RoboticsURJC/tfg-vdelatorre/memoria_tfg/portada/agradecimientos.tex

\cleardoublepage

\chapter*{Agradecimientos}

En primer lugar, quiero expresar mi gratitud a mi profesor, Julio Vega, por su apoyo y asesoramiento a lo largo de este proyecto. Sus conocimientos y recomendaciones fueron fundamentales para darle la dirección adecuada y obtener los resultados deseados.\\

A mis padres, gracias por su respaldo incondicional y por confiar en mí en cada etapa de mi formación académica.\\

Quiero agradecer también a mi hermana, mis amigos más cercanos y mi novia por sus ideas, consejos y por estar siempre ahí, brindándome su apoyo incondicional y motivación en todo momento.\\

Por último, me gustaría destacar la importancia de todos los recursos y fuentes que consulté durante la realización de este trabajo, así como de cualquier institución o persona que, de forma directa o indirecta, haya aportado a este proyecto.\\

Este trabajo es el resultado de cuatro años duros que no habrían resultado igual sin vosotros.\\
\ % Algo de separación...

\

\

\

\

\begin{flushright}
		\vspace{4.0 cm}
		\emph{A mi familia}\\
		\par
		\vspace{1.0 cm}
		Madrid, 2 de marzo de 2025\\ %\today
		\emph{Víctor de la Torre Rosa}
\end{flushright}

\thispagestyle{empty}
