RoboticsURJC/tfg-vdelatorre/memoria_tfg/portada/licencia.tex

% Este diseño se corresponde con la licencia CC-BY-NC-SA.
% Por supuesto, puedes poner la licencia que mejor se adapte al propósito de tu trabajo.
% Recuerda que, si no se especifica ninguna licencia, esta -como cualquier creación artística- pasaría a estar licenciada con todos los derechos reservados (copyright).

\cleardoublepage

\begin{flushright}
\begin{figure}
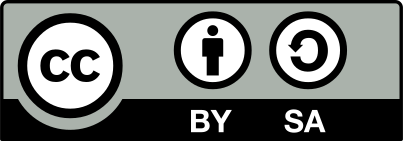
[picture p92: memoria_tfg/figs/by-sa.png]
 \ \ \ \ 
 \label{fig:cc} 
 \end{figure}
\end{flushright}

\

\

\

\noindent
Este trabajo se distribuye bajo los términos de la licencia internacional \href{http://creativecommons.org/licenses/by-sa/4.0/}{CC BY-SA International License} (Creative Commons Attribution-ShareAlike 4.0). Usted es libre de \textit{(a) compartir}: copiar y redistribuir el material en cualquier medio o formato para cualquier propósito, incluso comercialmente; y \textit{(b) adaptar}: remezclar, transformar y construir a partir del material para cualquier propósito, incluso comercialmente. La licenciante no puede revocar estas libertades en tanto usted siga los términos de la licencia:

\begin{itemize}
\item \textit{Atribución}. Usted debe dar \href{https://creativecommons.org/licenses/by-sa/4.0/deed.es#ref-appropriate-credit}{crédito de manera adecuada}, brindar un enlace a la licencia, e indicar \href{https://creativecommons.org/licenses/by-sa/4.0/deed.es#ref-indicate-changes}{si se han realizado cambios}. Puede hacerlo en cualquier forma razonable, pero no de forma tal que sugiera que usted o su uso tienen el apoyo de la licenciante.
\item \textit{Compartir igual}. Si remezcla, transforma o crea a partir del material, debe distribuir su contribución bajo la \href{https://creativecommons.org/licenses/by-sa/4.0/deed.es#ref-same-license}{misma licencia} del original.\\
No hay restricciones adicionales — No puede aplicar términos legales ni \href{https://creativecommons.org/licenses/by-sa/4.0/deed.es#ref-technological-measures}{medidas tecnológicas} que restrinjan legalmente a otras a hacer cualquier uso permitido por la licencia.
\end{itemize}

\begin{flushright}
		\vspace{7.0 cm}
		\emph{Documento de} \textbf{Víctor de la Torre Rosa}. % TODO: pon aquí tu nombre cuando hagas el documento
\end{flushright}
