RoboticsURJC/tfg-vdelatorre/Imagenes/2025-01-02-201215_1920x1080_scrot.png

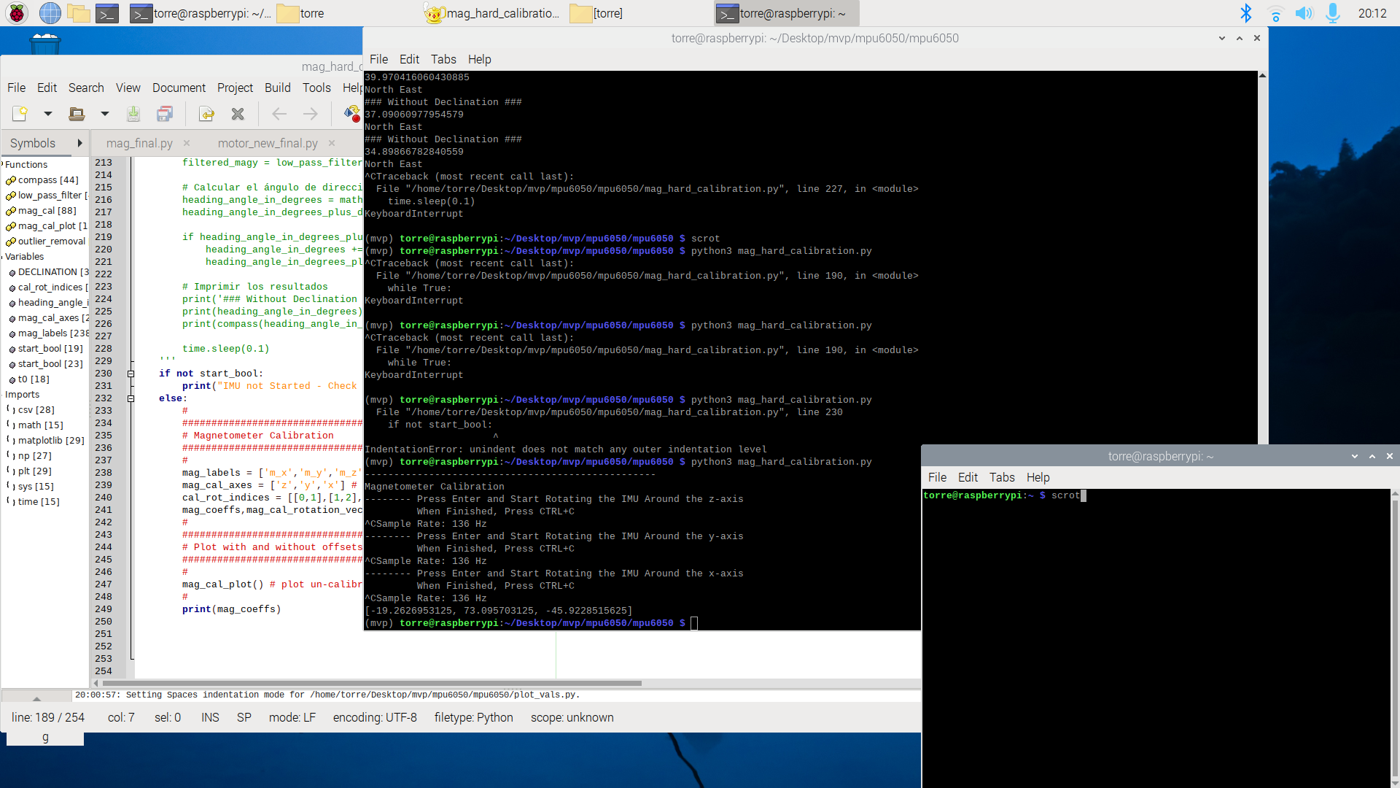
Imagenes/2025-01-02-201215_1920x1080_scrot.png
