RoboticsURJC/tfg-vdelatorre/Imagenes/aprox_pos_rasp.png

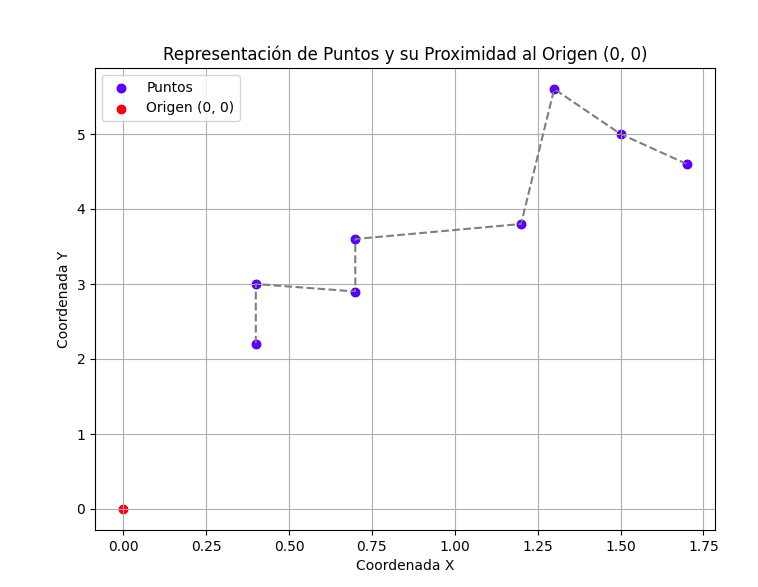
Imagenes/aprox_pos_rasp.png
