RoboticsURJC/tfg-vdelatorre/Imagenes/aps.jpeg

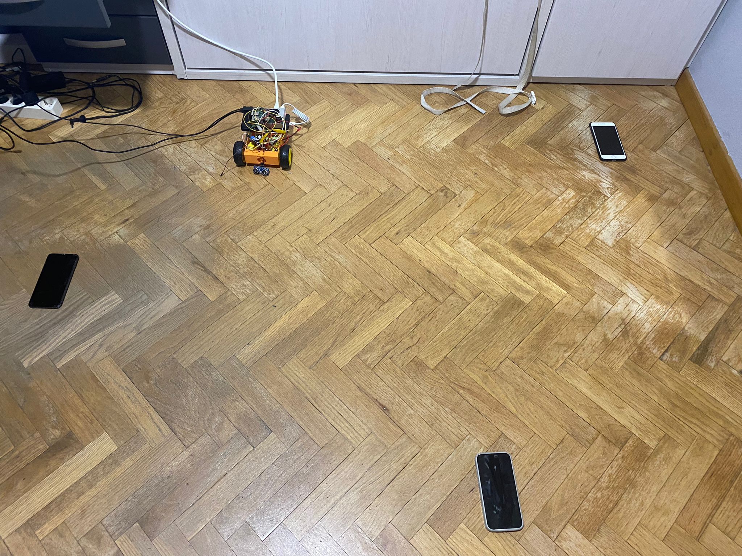
Imagenes/aps.jpeg
