RoboticsURJC/tfg-vdelatorre/Imagenes/astar2.png

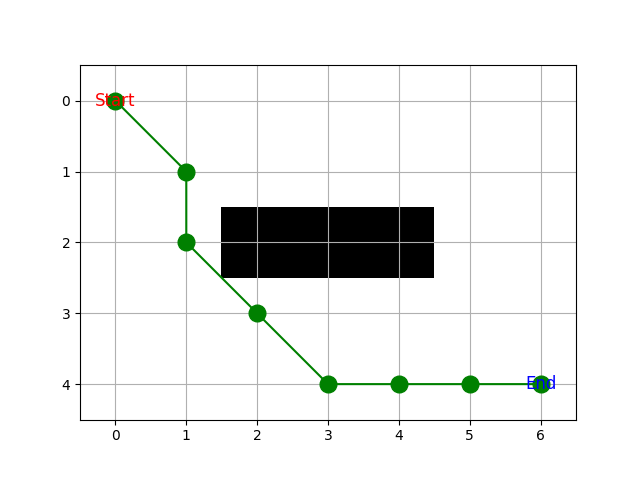
Imagenes/astar2.png
