RoboticsURJC/tfg-vdelatorre/Imagenes/astar3.png

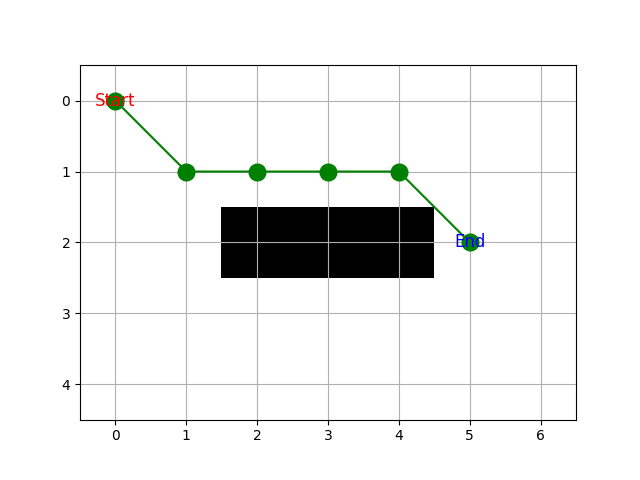
Imagenes/astar3.png
