RoboticsURJC/tfg-vdelatorre/Imagenes/astar5.png

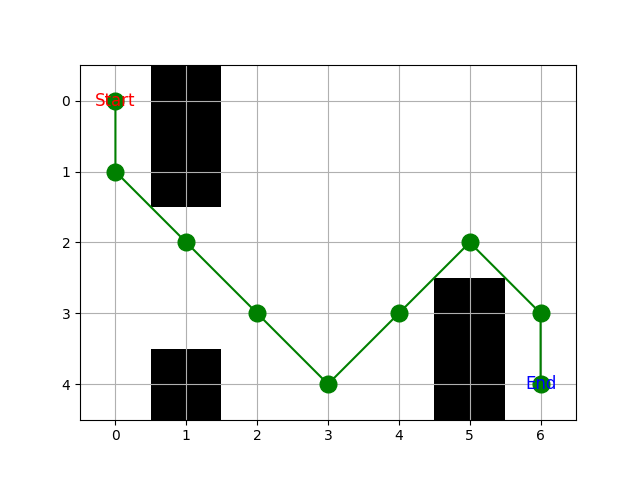
Imagenes/astar5.png
