RoboticsURJC/tfg-vdelatorre/Imagenes/astar.png

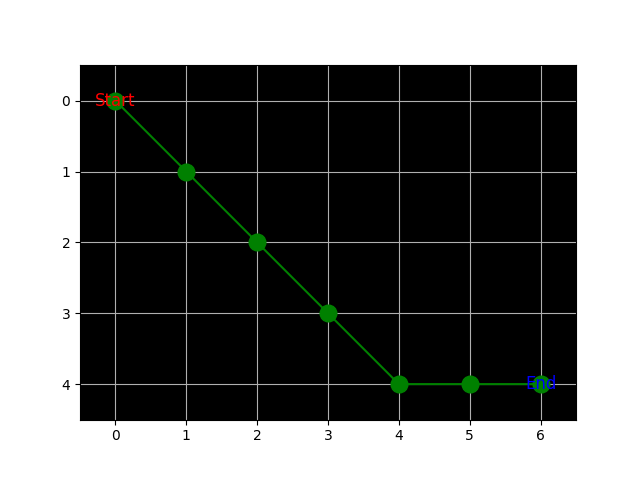
Imagenes/astar.png
