RoboticsURJC/tfg-vdelatorre/Imagenes/base_batería.png

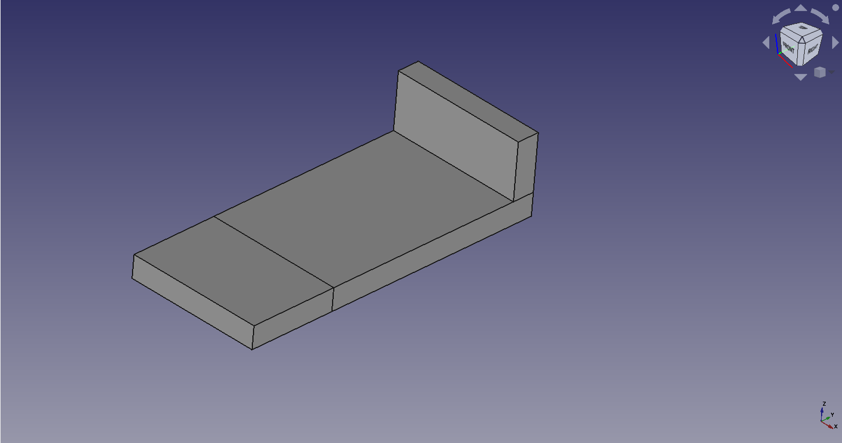
Imagenes/base_batería.png
