RoboticsURJC/tfg-vdelatorre/Imagenes/base_inicial_motor.png

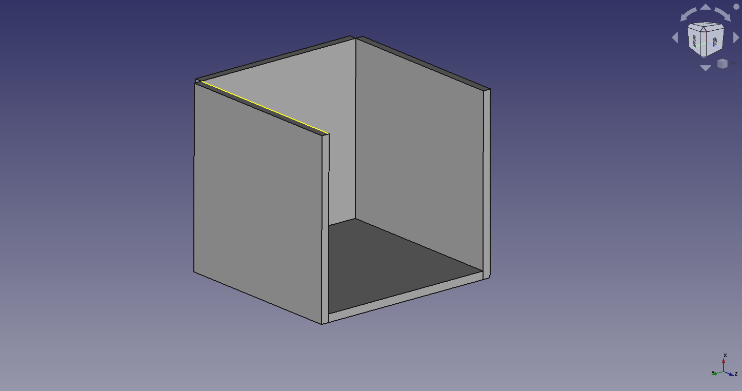
Imagenes/base_inicial_motor.png
