RoboticsURJC/tfg-vdelatorre/Imagenes/binary_text.png

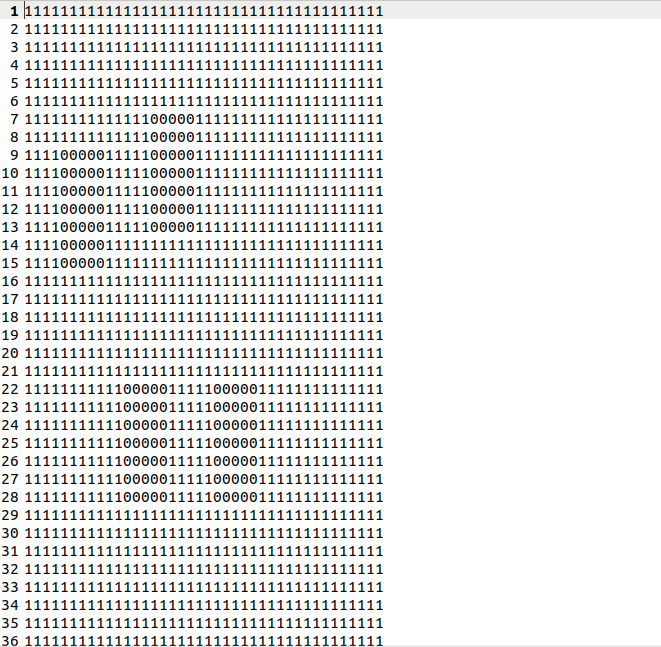
Imagenes/binary_text.png
