RoboticsURJC/tfg-vdelatorre/Imagenes/blog_2020_Raspberry_Pi4_Pi3B_00.jpg

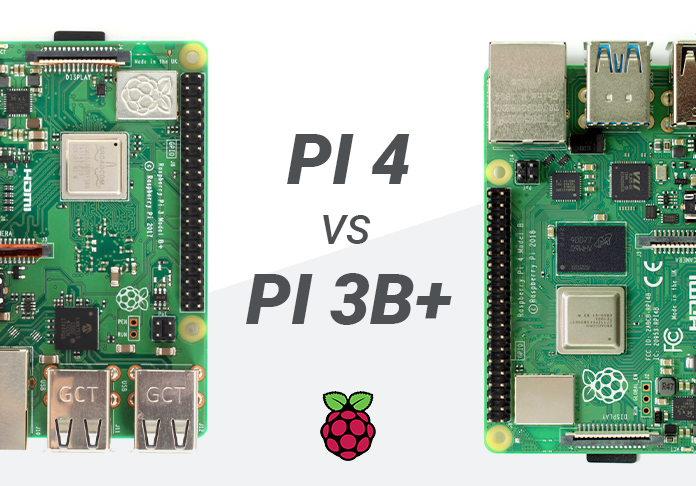
Imagenes/blog_2020_Raspberry_Pi4_Pi3B_00.jpg
