RoboticsURJC/tfg-vdelatorre/Imagenes/bola_loca.jpeg

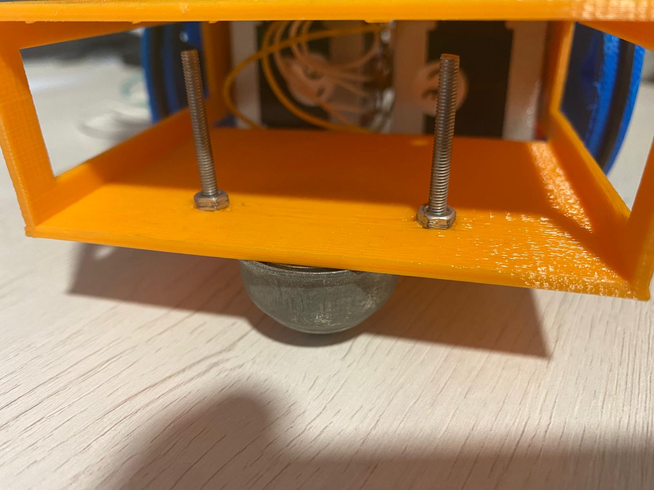
Imagenes/bola_loca.jpeg
