RoboticsURJC/tfg-vdelatorre/Imagenes/confusion_matrix.png

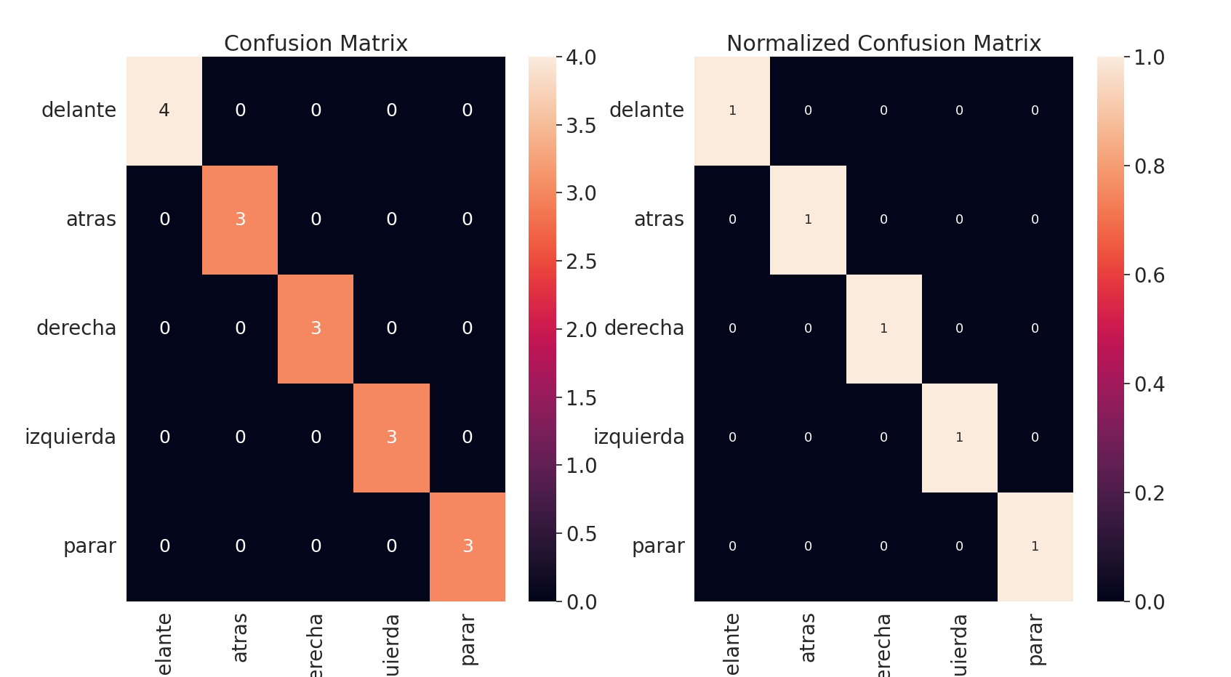
Imagenes/confusion_matrix.png
