RoboticsURJC/tfg-vdelatorre/Imagenes/dataset_add.png

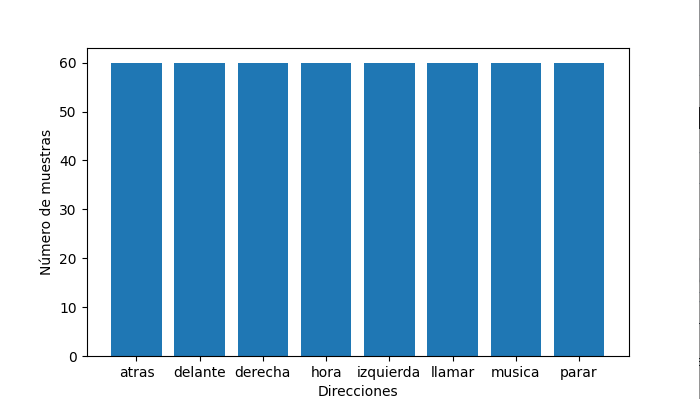
Imagenes/dataset_add.png
