RoboticsURJC/tfg-vdelatorre/Imagenes/datos_revista.png

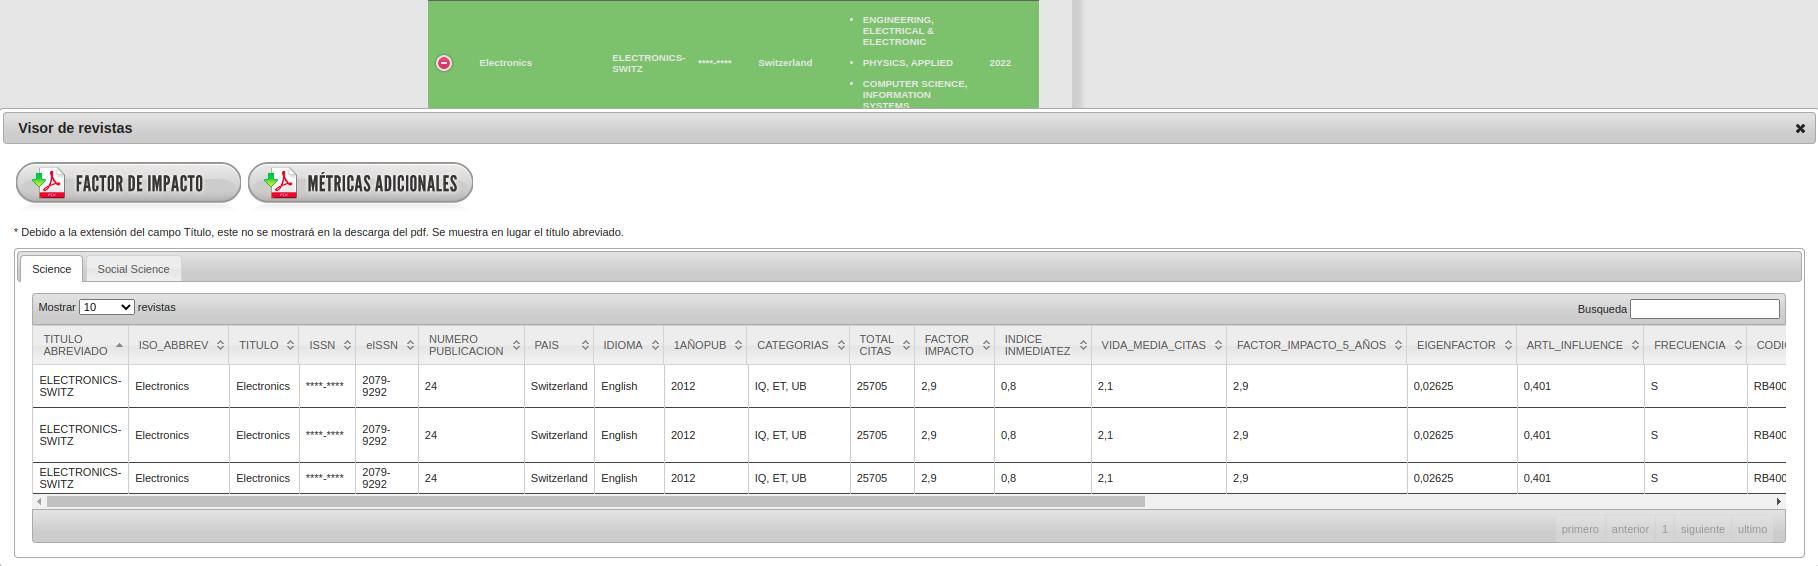
Imagenes/datos_revista.png
