RoboticsURJC/tfg-vdelatorre/Imagenes/driver_motor.jpeg

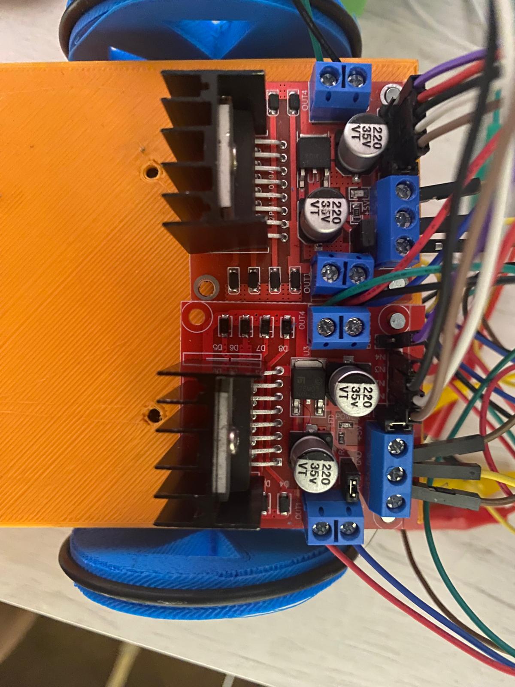
Imagenes/driver_motor.jpeg
