RoboticsURJC/tfg-vdelatorre/Imagenes/escalado_minmax_estandar.png

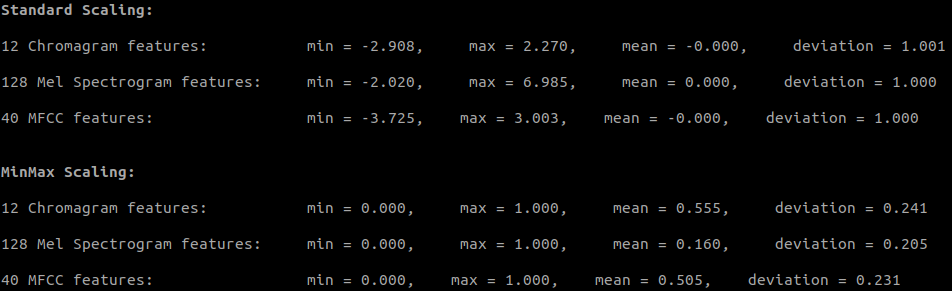
Imagenes/escalado_minmax_estandar.png
