RoboticsURJC/tfg-vdelatorre/Imagenes/fecyt.png

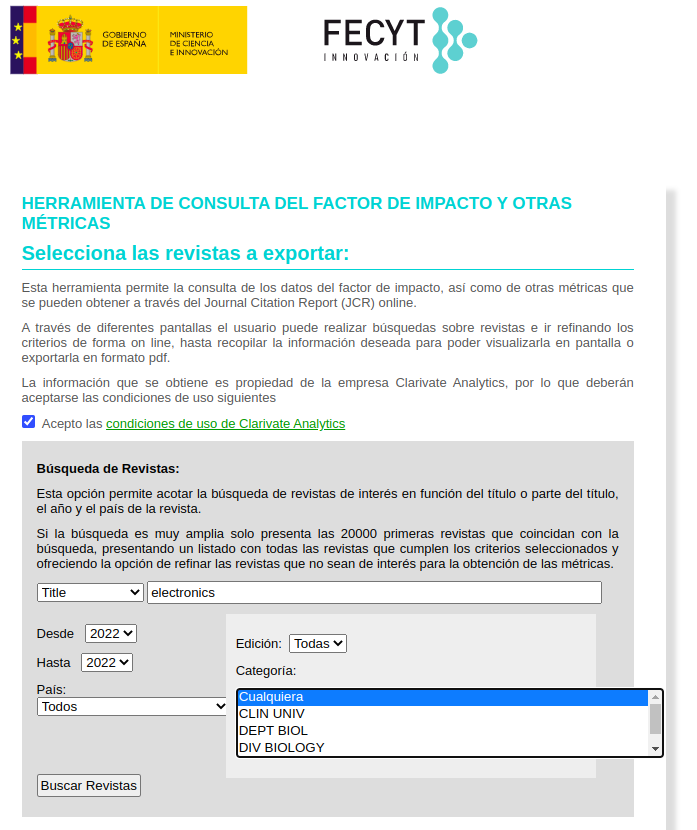
Imagenes/fecyt.png
