RoboticsURJC/tfg-vdelatorre/Imagenes/giroscopio.jpg

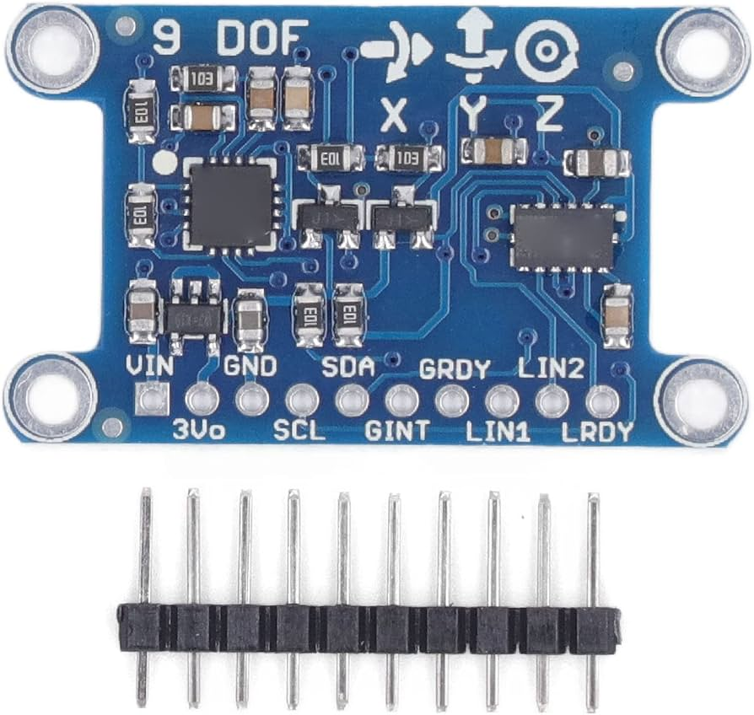
Imagenes/giroscopio.jpg
