RoboticsURJC/tfg-vdelatorre/Imagenes/google_scholar.png

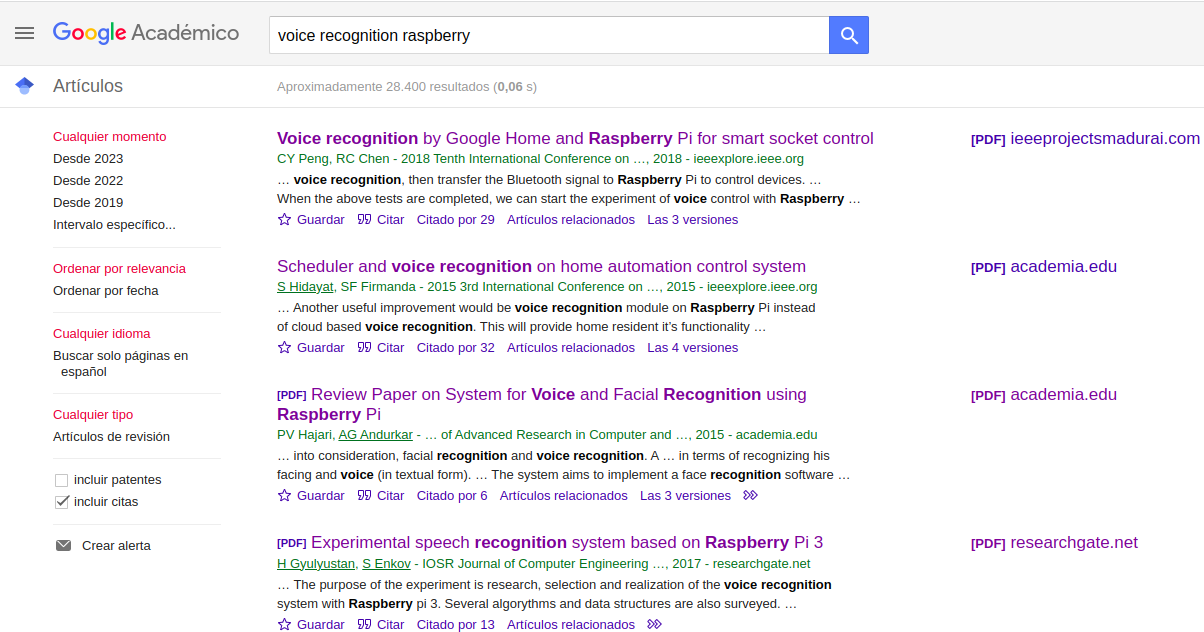
Imagenes/google_scholar.png
