RoboticsURJC/tfg-vdelatorre/Imagenes/gyros.png

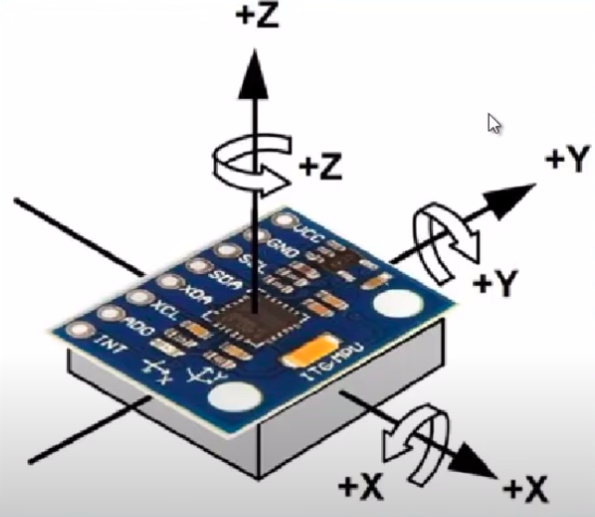
Imagenes/gyros.png
