RoboticsURJC/tfg-vdelatorre/Imagenes/imagen_motor_base.JPG

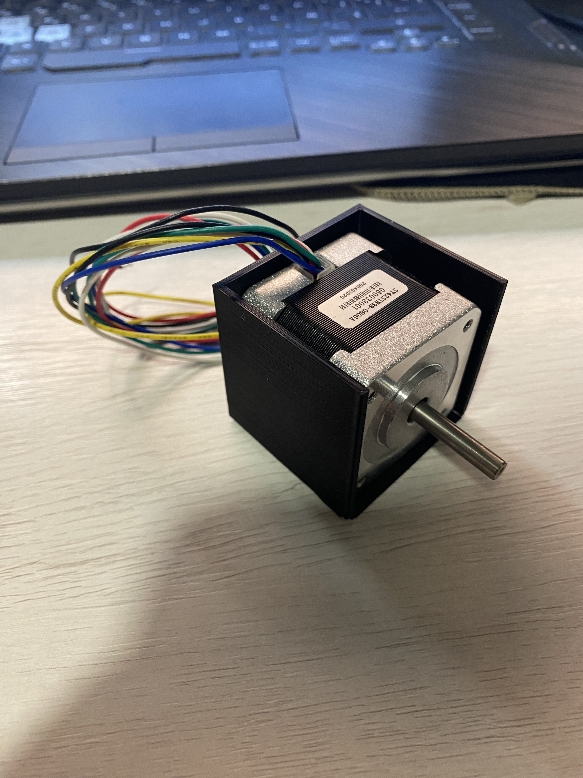
Imagenes/imagen_motor_base.JPG
