RoboticsURJC/tfg-vdelatorre/Imagenes/junta_rueda.jpeg

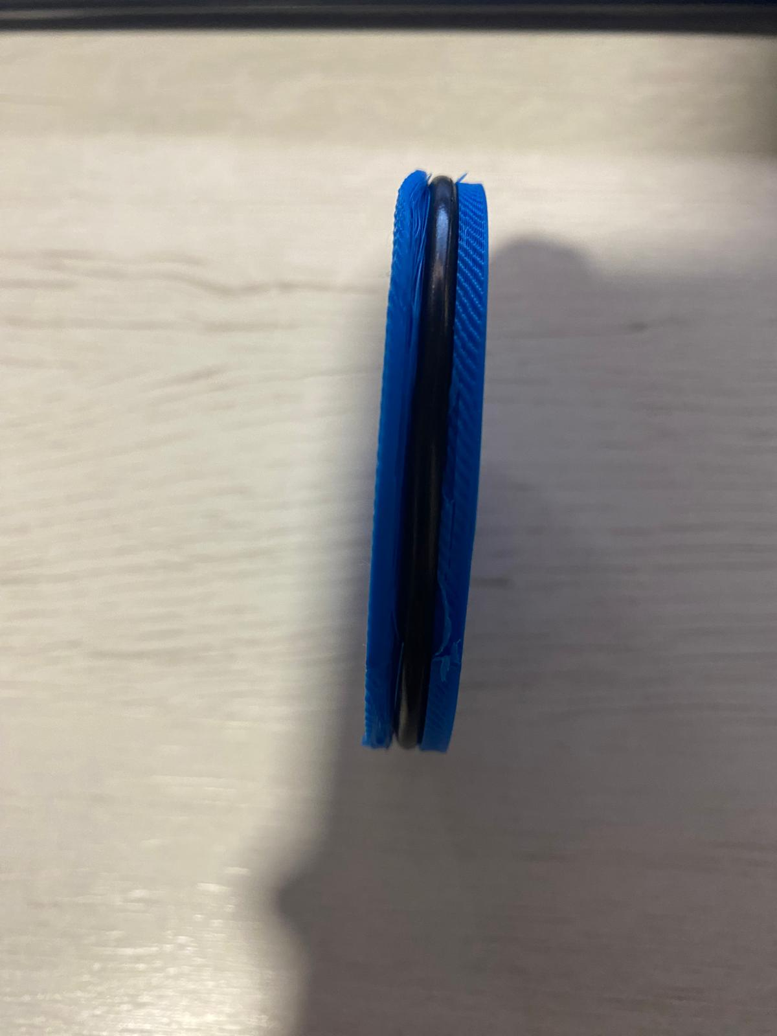
Imagenes/junta_rueda.jpeg
