RoboticsURJC/tfg-vdelatorre/Imagenes/l298n_bipolar_stepper_bb.png

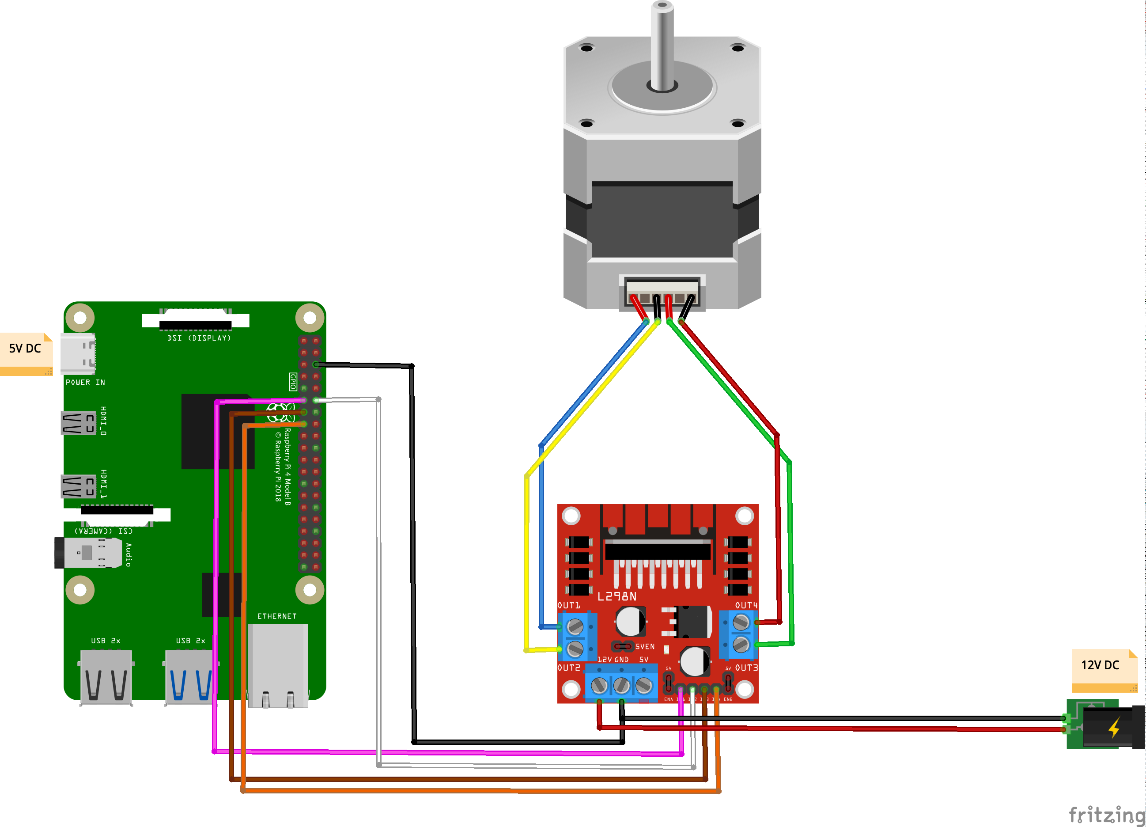
Imagenes/l298n_bipolar_stepper_bb.png
