RoboticsURJC/tfg-vdelatorre/Imagenes/map.png

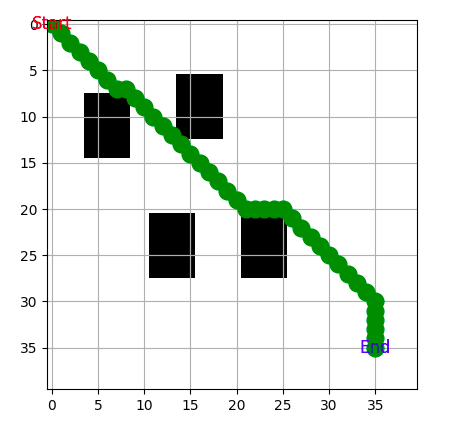
Imagenes/map.png
