RoboticsURJC/tfg-vdelatorre/Imagenes/map_color2.png

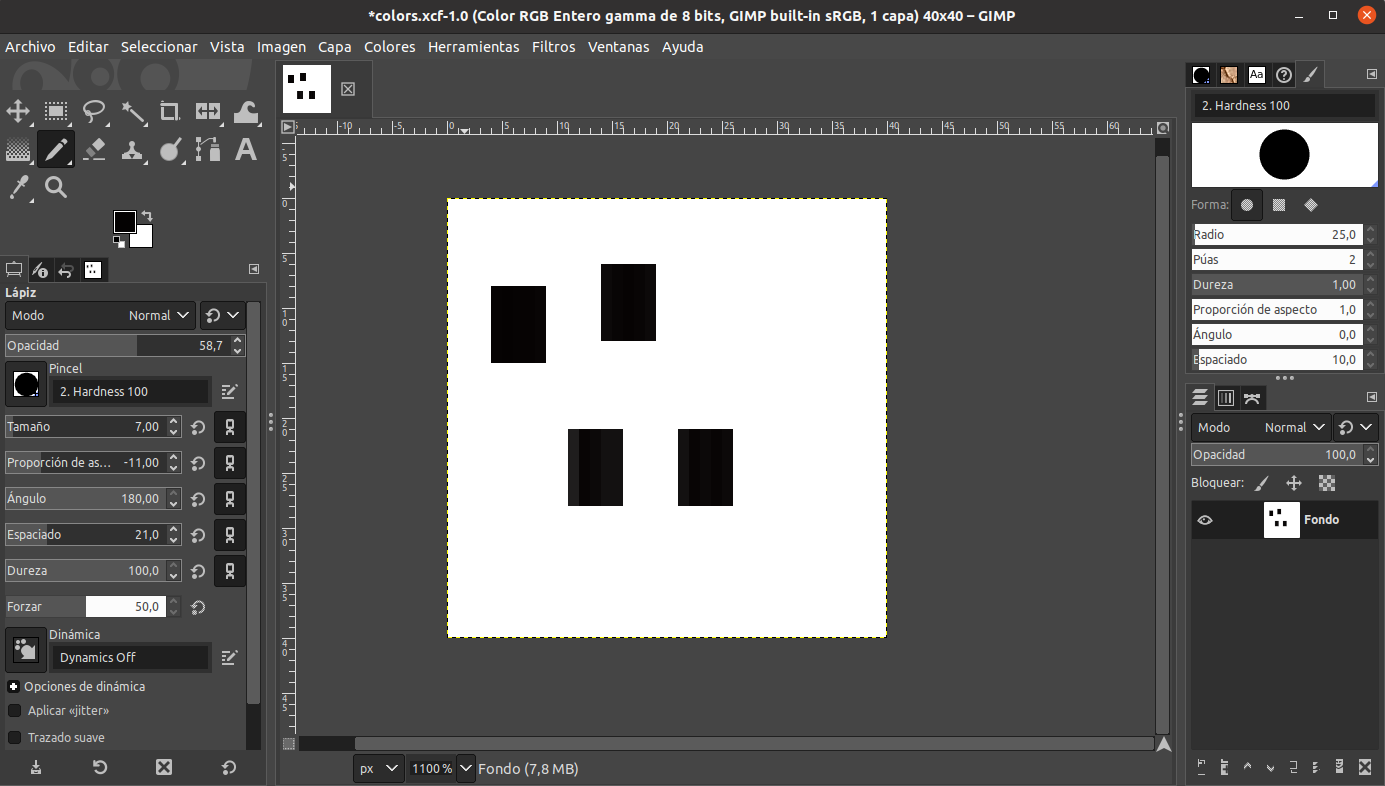
Imagenes/map_color2.png
