RoboticsURJC/tfg-vdelatorre/Imagenes/map_color.png

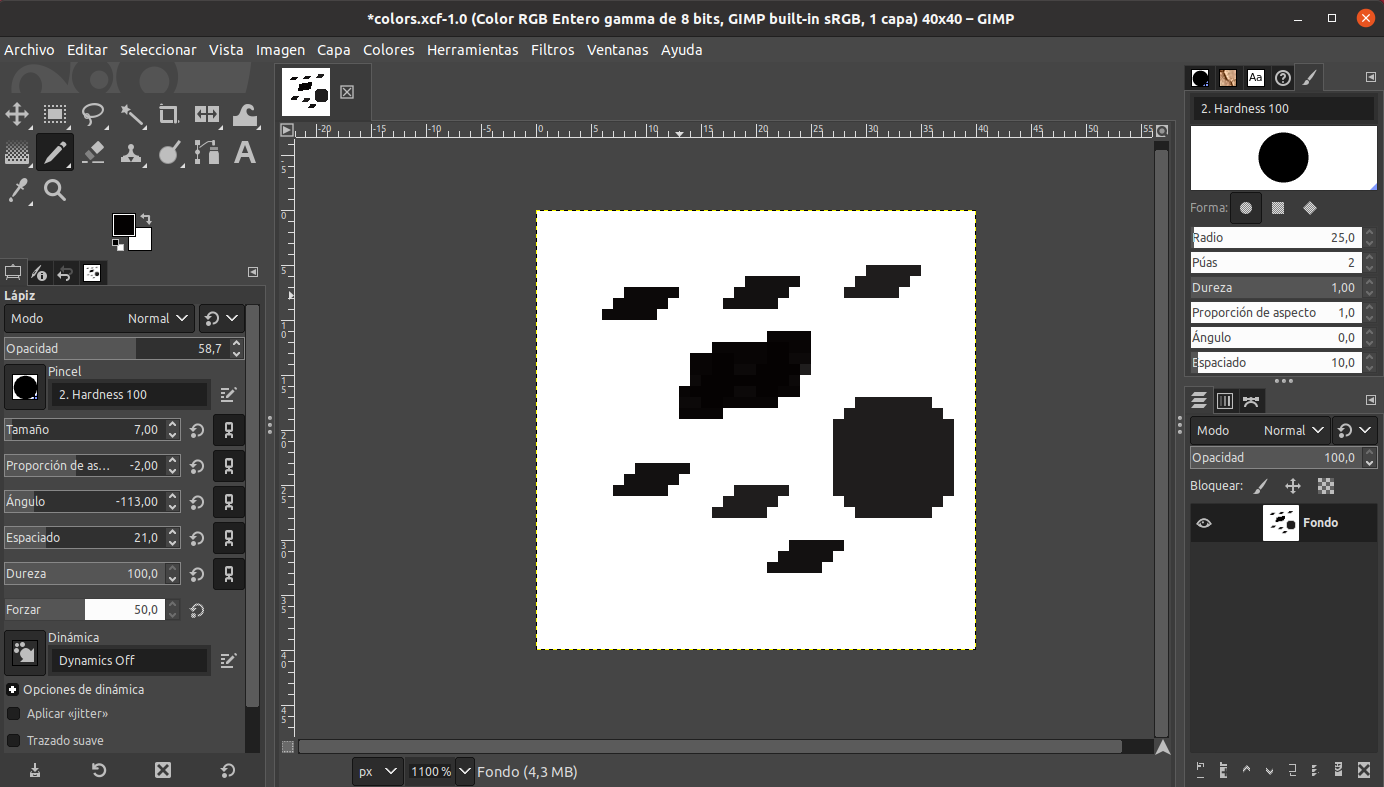
Imagenes/map_color.png
