RoboticsURJC/tfg-vdelatorre/Imagenes/matrix_features.png

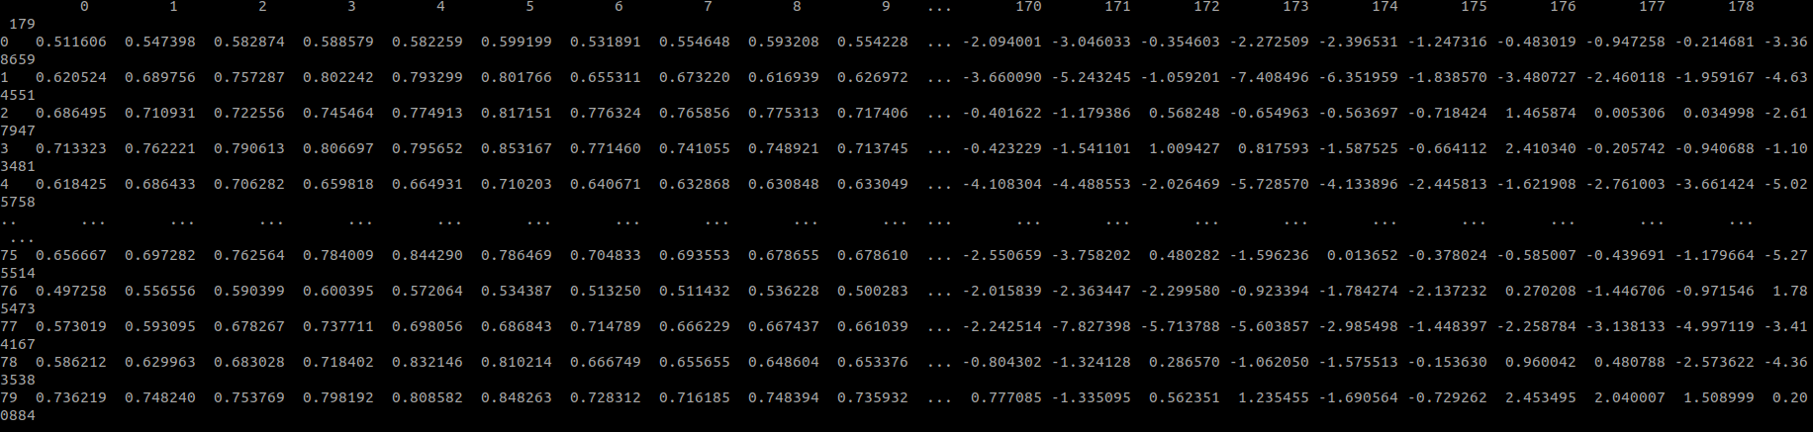
Imagenes/matrix_features.png
