RoboticsURJC/tfg-vdelatorre/Imagenes/matriz_confusion.png

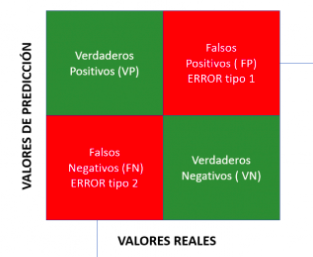
Imagenes/matriz_confusion.png
