RoboticsURJC/tfg-vdelatorre/Imagenes/modelo_silla_ruedas.png

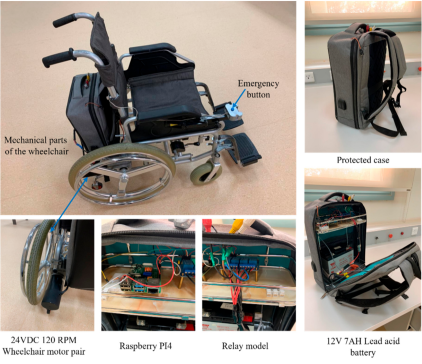
Imagenes/modelo_silla_ruedas.png
