RoboticsURJC/tfg-vdelatorre/Imagenes/motor1.jpg

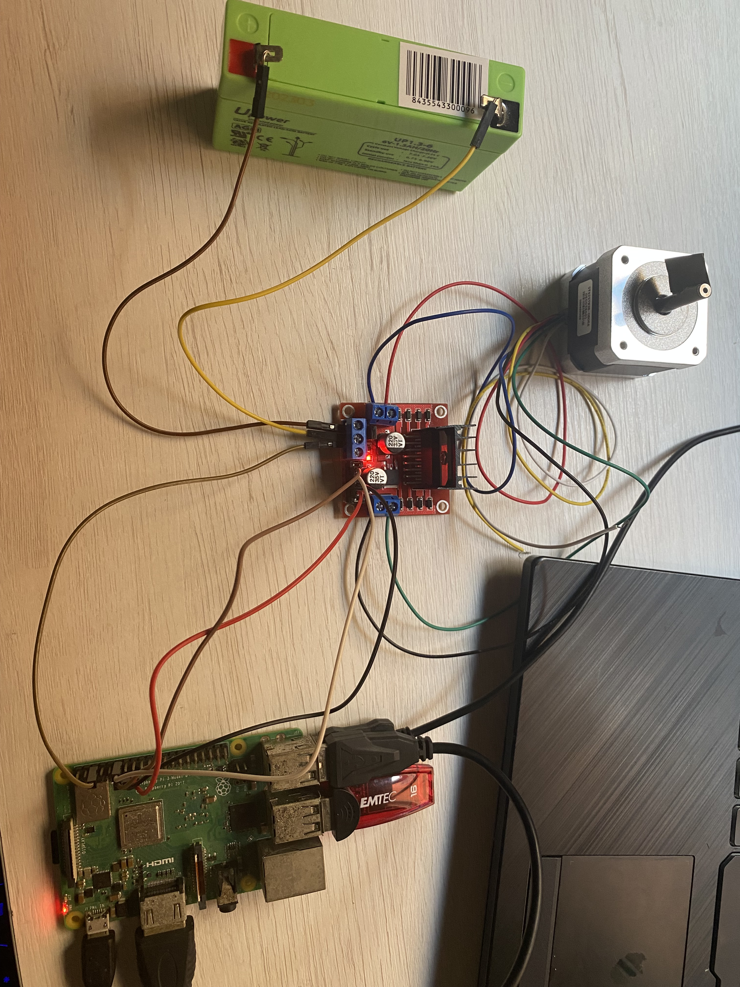
Imagenes/motor1.jpg
