RoboticsURJC/tfg-vdelatorre/Imagenes/motor2.jpg

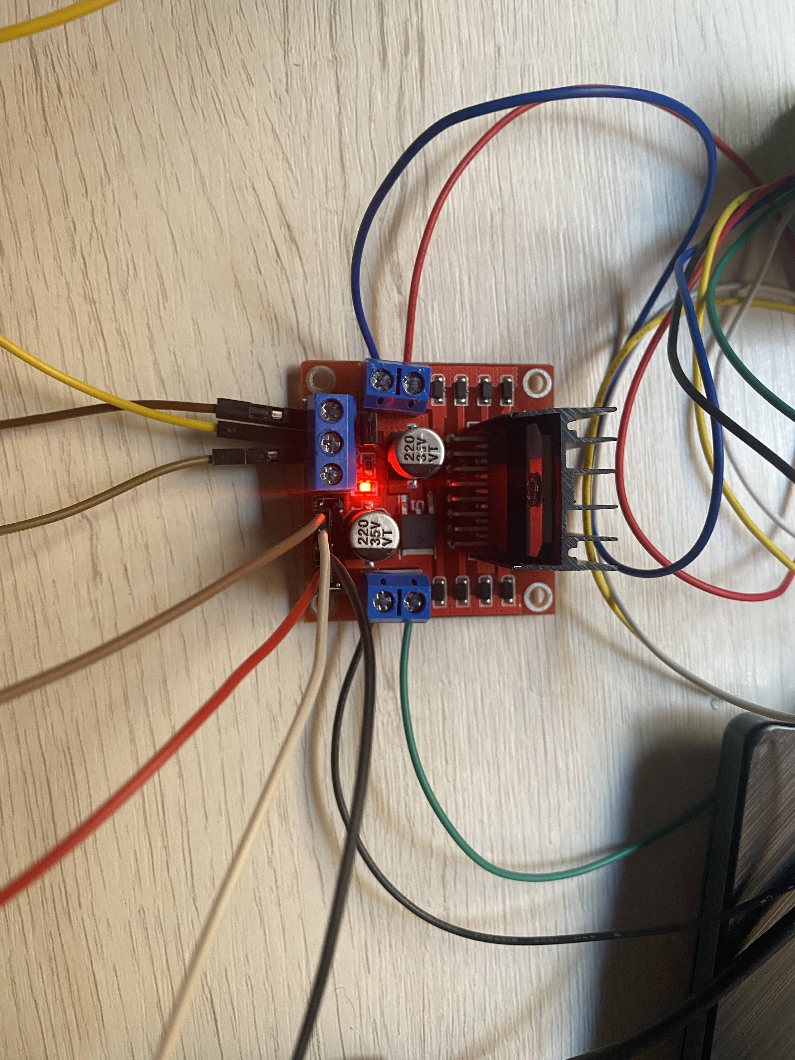
Imagenes/motor2.jpg
