RoboticsURJC/tfg-vdelatorre/Imagenes/motor3.jpg

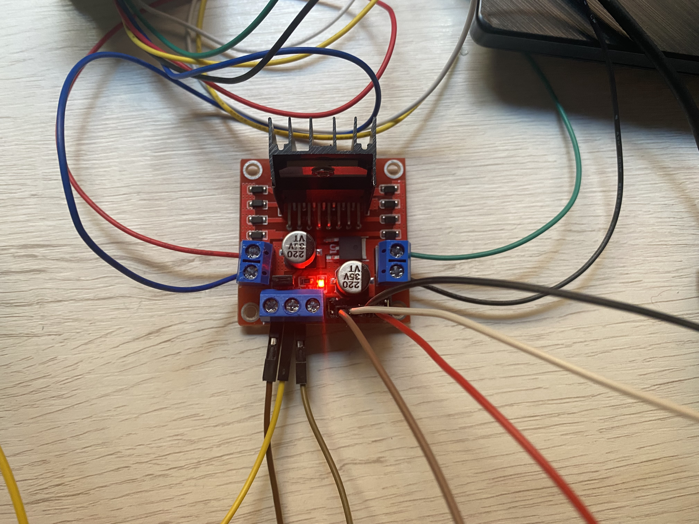
Imagenes/motor3.jpg
