RoboticsURJC/tfg-vdelatorre/Imagenes/motor4.jpg

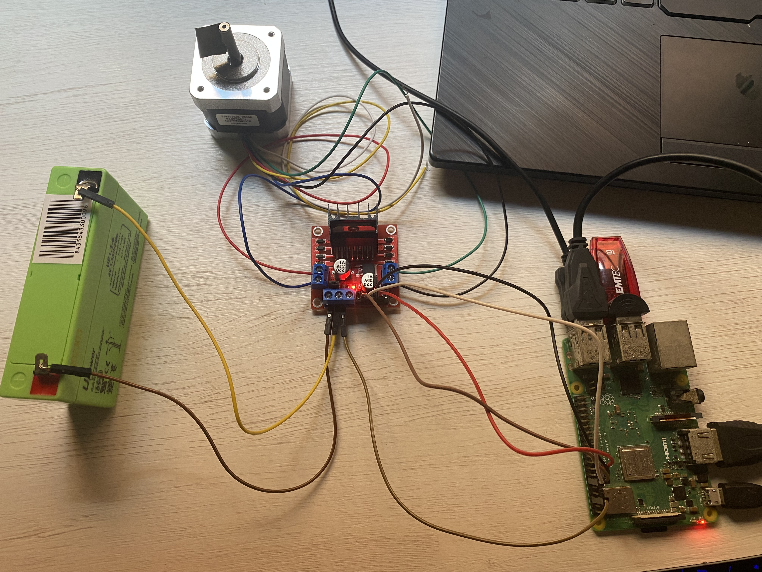
Imagenes/motor4.jpg
