RoboticsURJC/tfg-vdelatorre/Imagenes/motor_montura.png

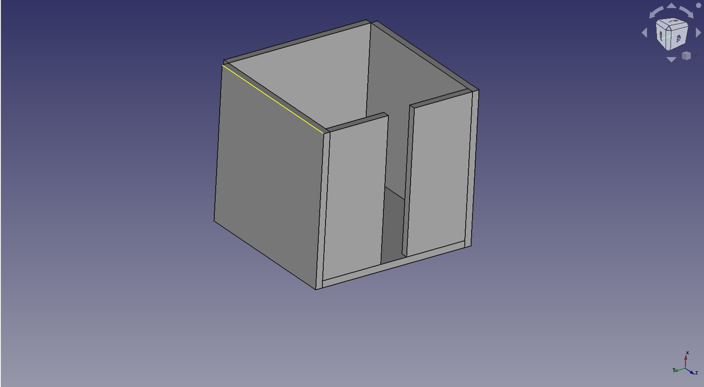
Imagenes/motor_montura.png
