RoboticsURJC/tfg-vdelatorre/Imagenes/motor_paso_a_paso.JPG

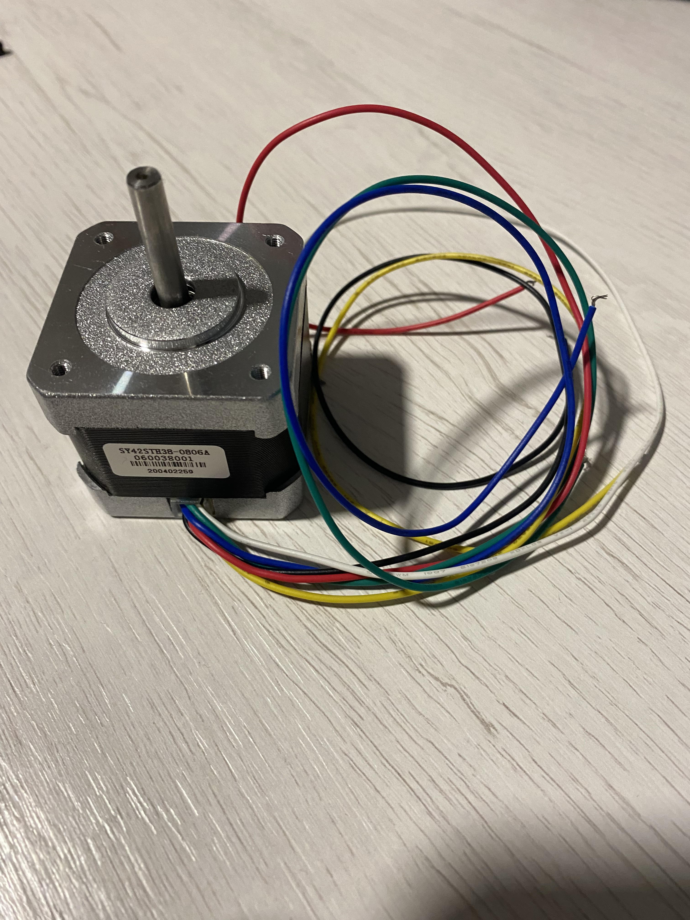
Imagenes/motor_paso_a_paso.JPG
