RoboticsURJC/tfg-vdelatorre/Imagenes/muestras.png

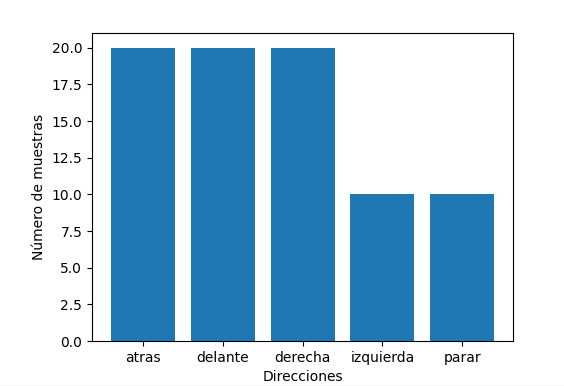
Imagenes/muestras.png
