RoboticsURJC/tfg-vdelatorre/Imagenes/multimetro_200.JPG

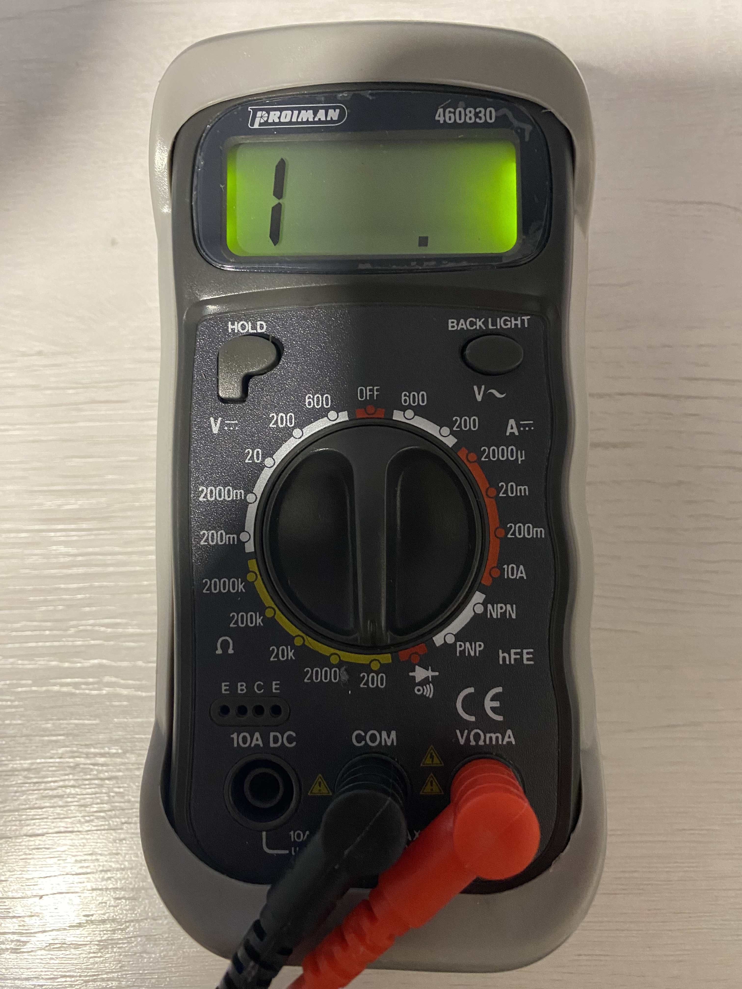
Imagenes/multimetro_200.JPG
