RoboticsURJC/tfg-vdelatorre/Imagenes/multimetro_continuidad.JPG

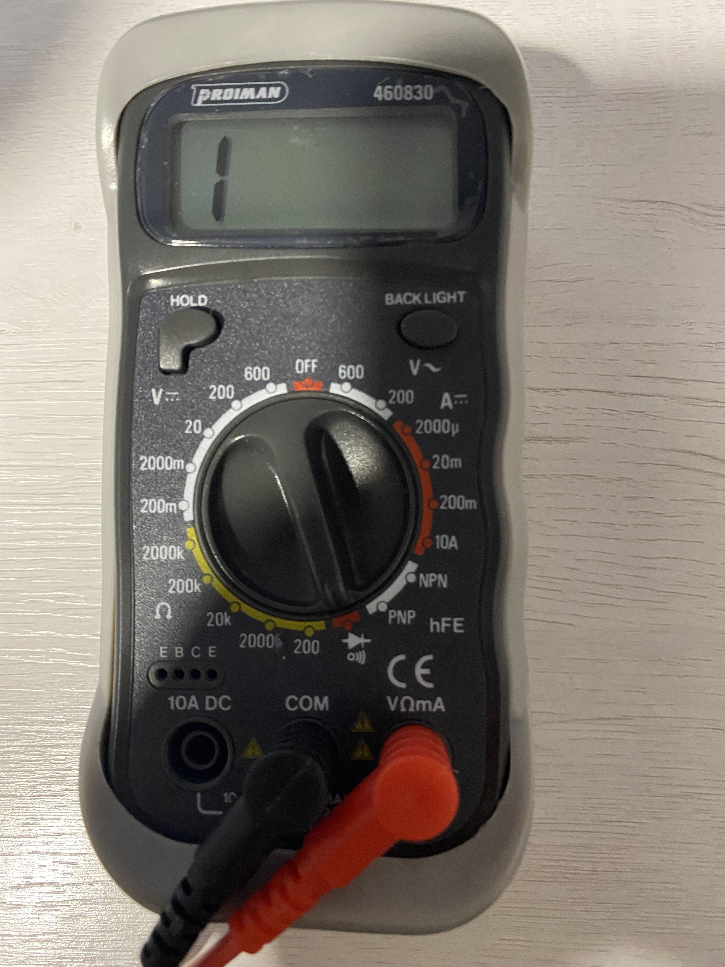
Imagenes/multimetro_continuidad.JPG
