RoboticsURJC/tfg-vdelatorre/Imagenes/pieza_superior_apertura_cables.png

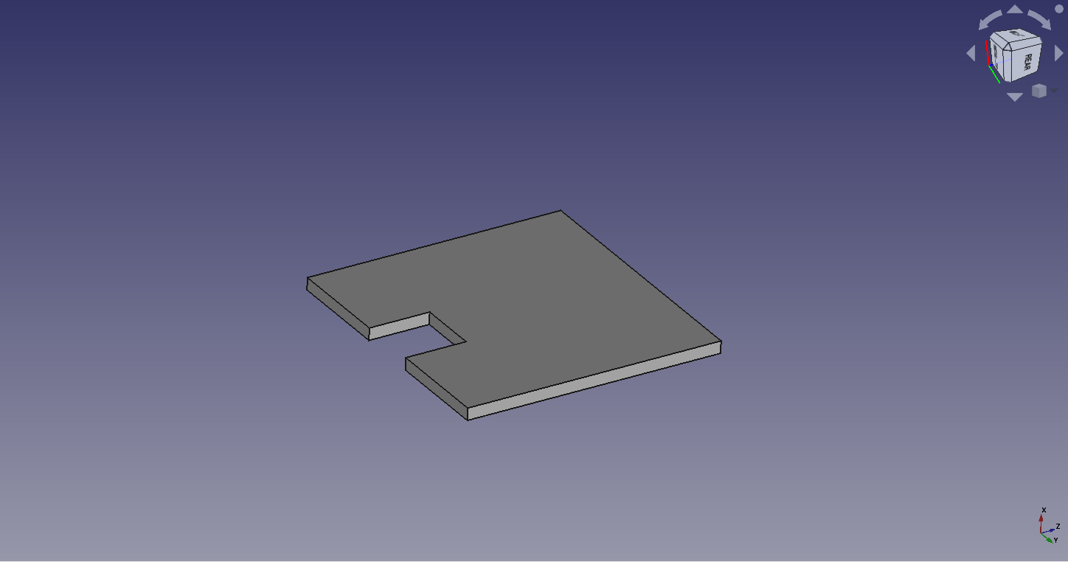
Imagenes/pieza_superior_apertura_cables.png
