RoboticsURJC/tfg-vdelatorre/Imagenes/pieza_tubo.jpeg

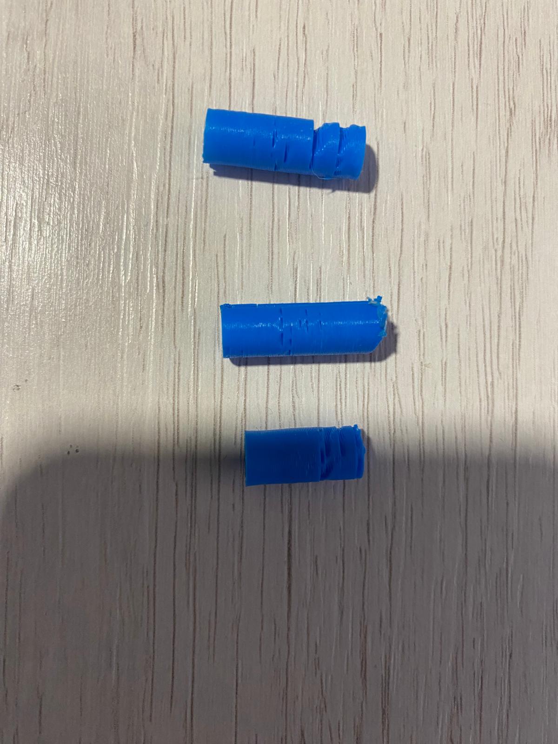
Imagenes/pieza_tubo.jpeg
