RoboticsURJC/tfg-vdelatorre/Imagenes/poses.png

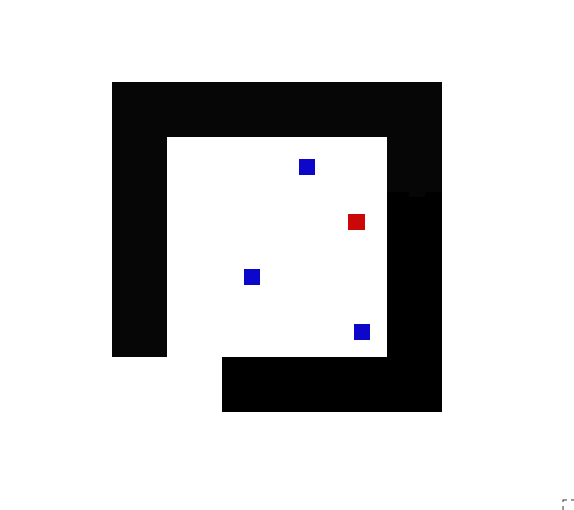
Imagenes/poses.png
