RoboticsURJC/tfg-vdelatorre/Imagenes/robot1.jpeg

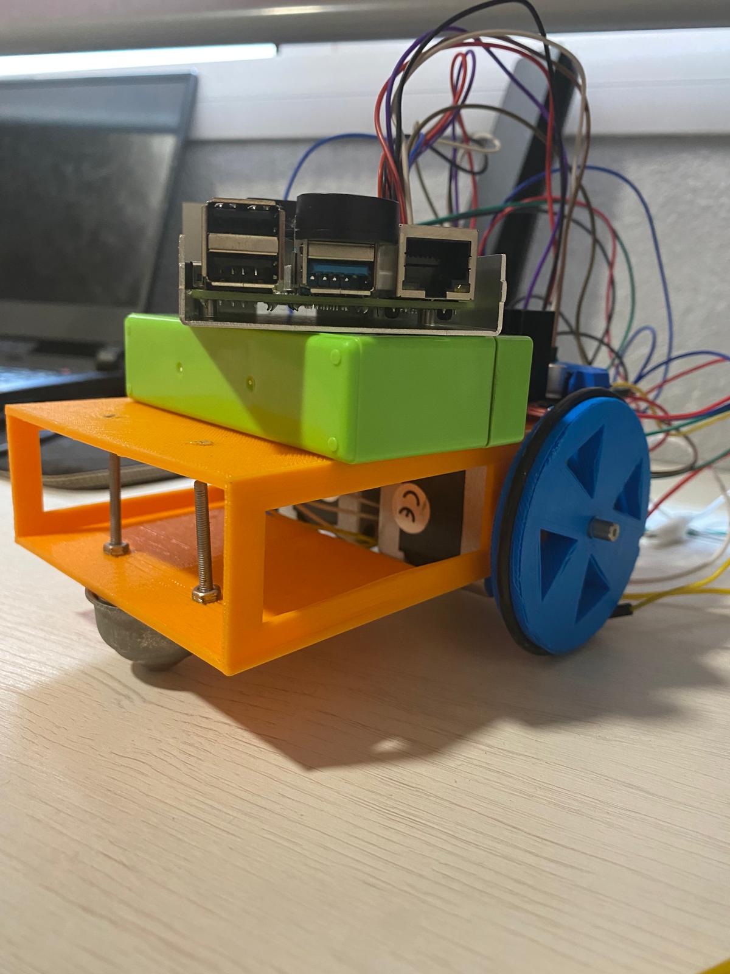
Imagenes/robot1.jpeg
