RoboticsURJC/tfg-vdelatorre/Imagenes/robot2.jpeg

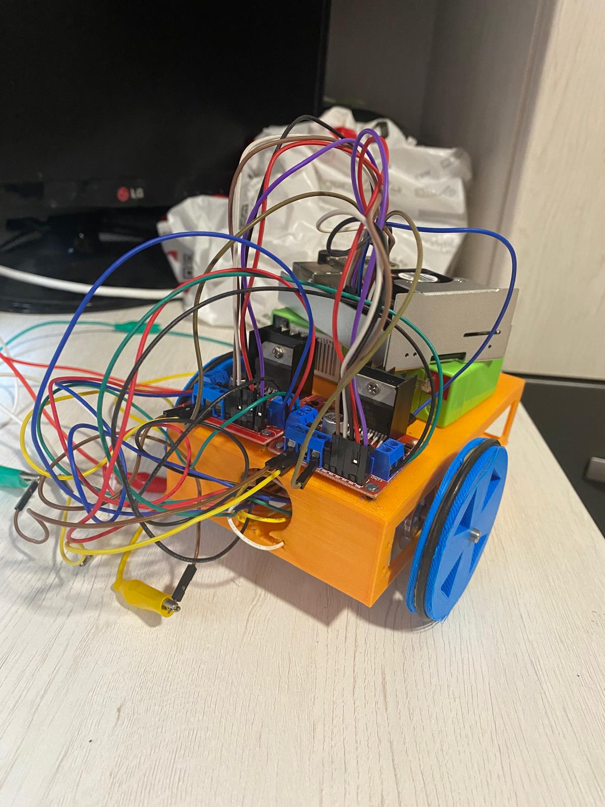
Imagenes/robot2.jpeg
