RoboticsURJC/tfg-vdelatorre/Imagenes/robot3.jpeg

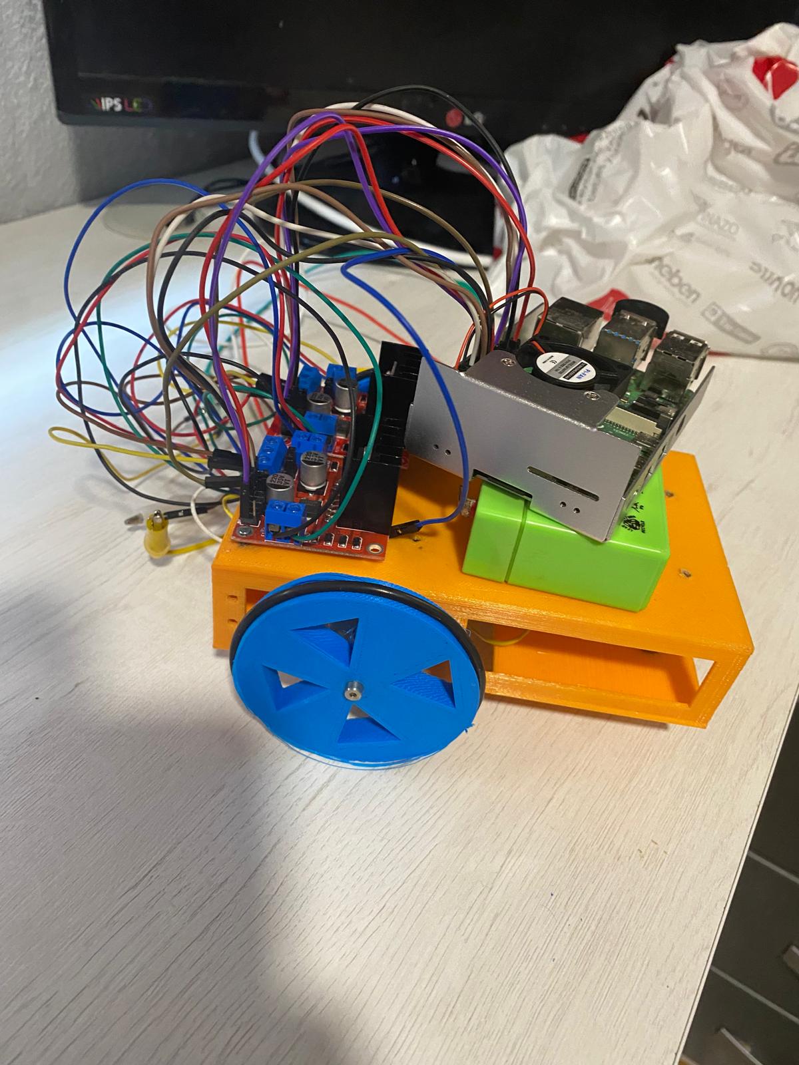
Imagenes/robot3.jpeg
