RoboticsURJC/tfg-vdelatorre/Imagenes/robot4.jpeg

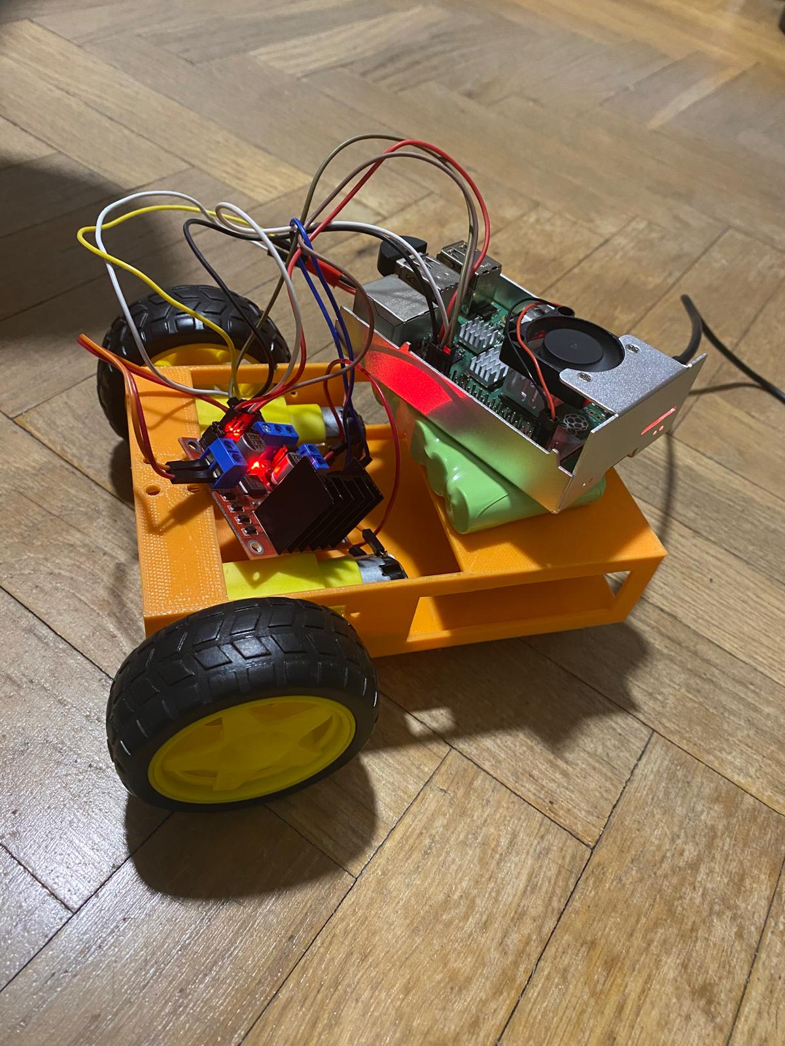
Imagenes/robot4.jpeg
