RoboticsURJC/tfg-vdelatorre/Imagenes/robot5.jpeg

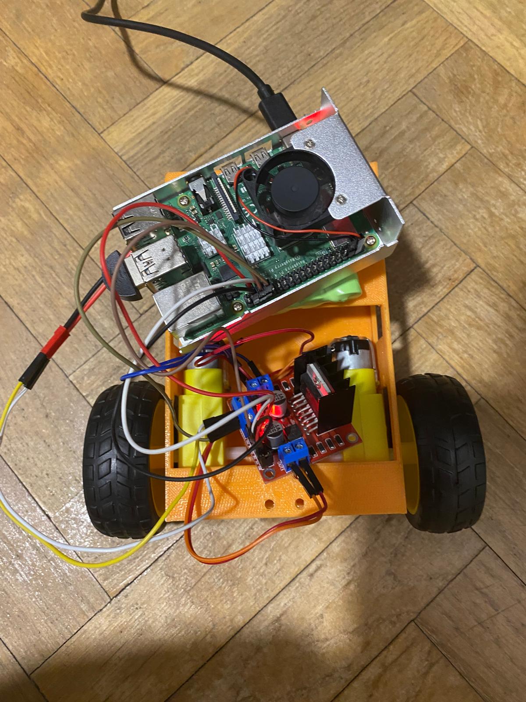
Imagenes/robot5.jpeg
