RoboticsURJC/tfg-vdelatorre/Imagenes/rrt1.png

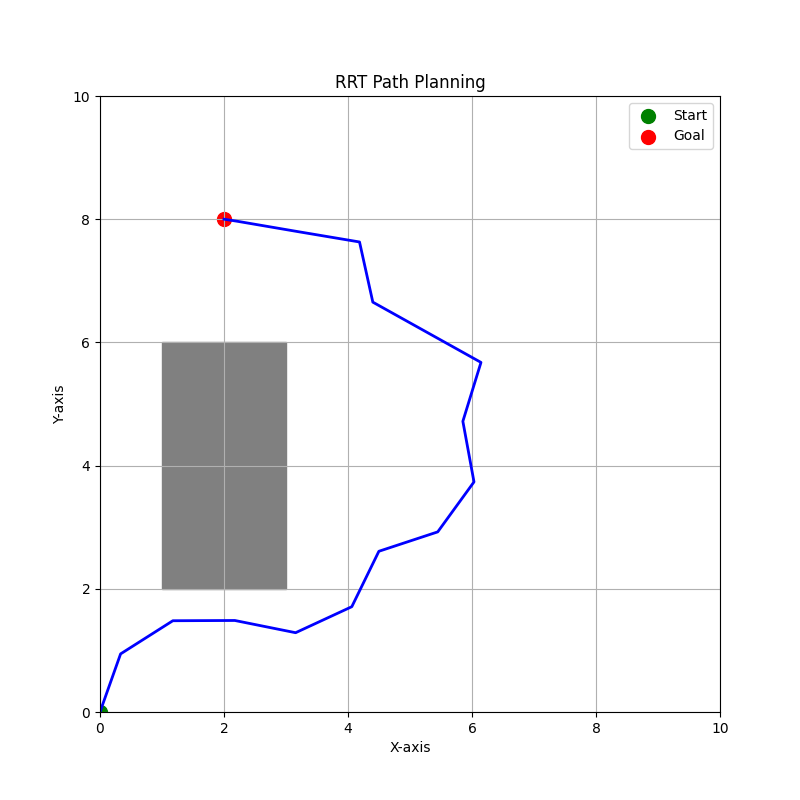
Imagenes/rrt1.png
