RoboticsURJC/tfg-vdelatorre/Imagenes/rrt2.png

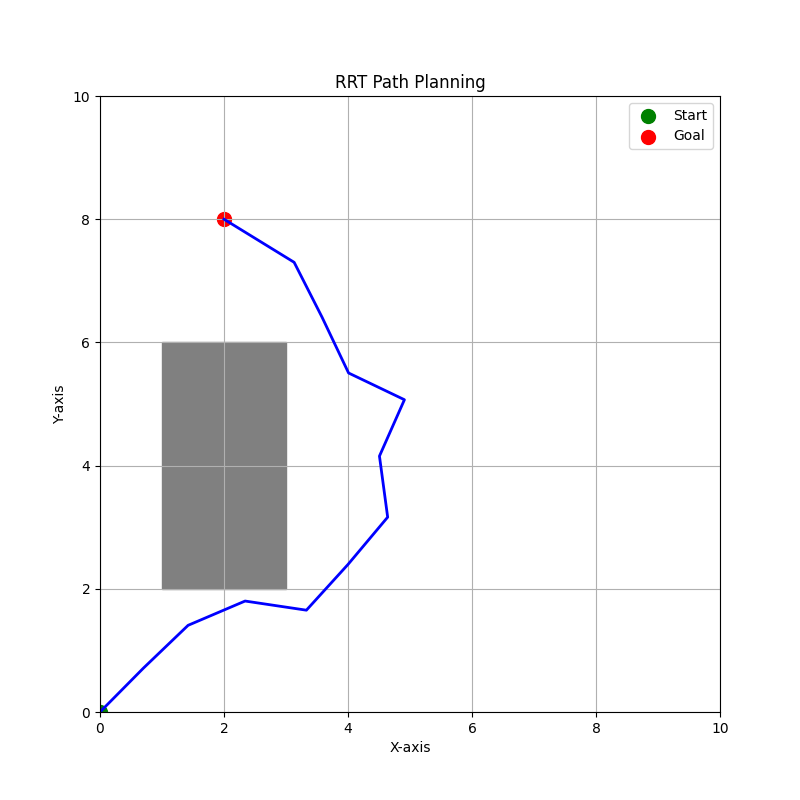
Imagenes/rrt2.png
