RoboticsURJC/tfg-vdelatorre/Imagenes/rrt3.png

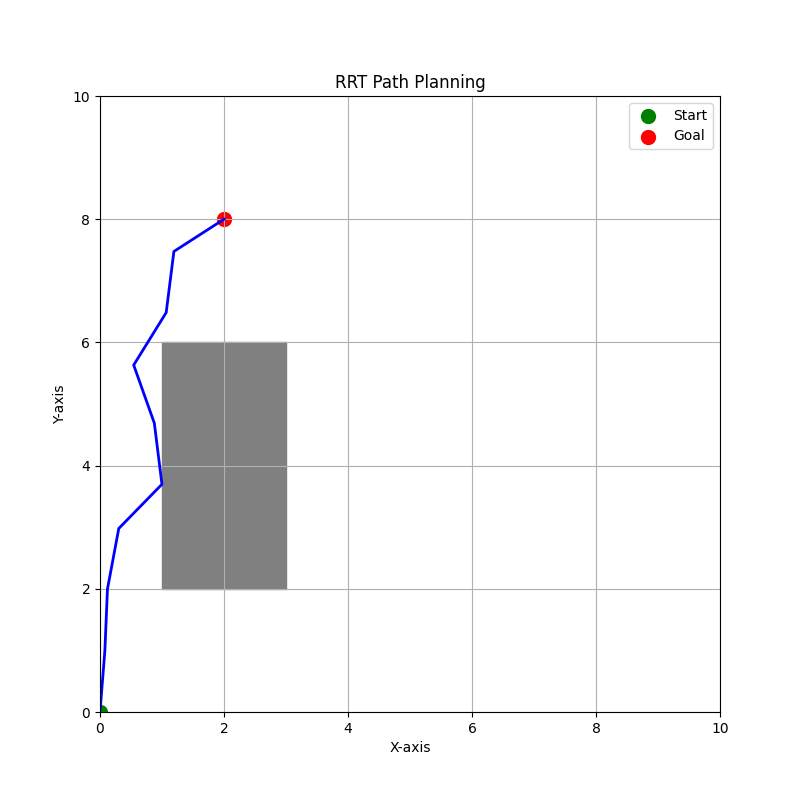
Imagenes/rrt3.png
