RoboticsURJC/tfg-vdelatorre/Imagenes/rueda.jpeg

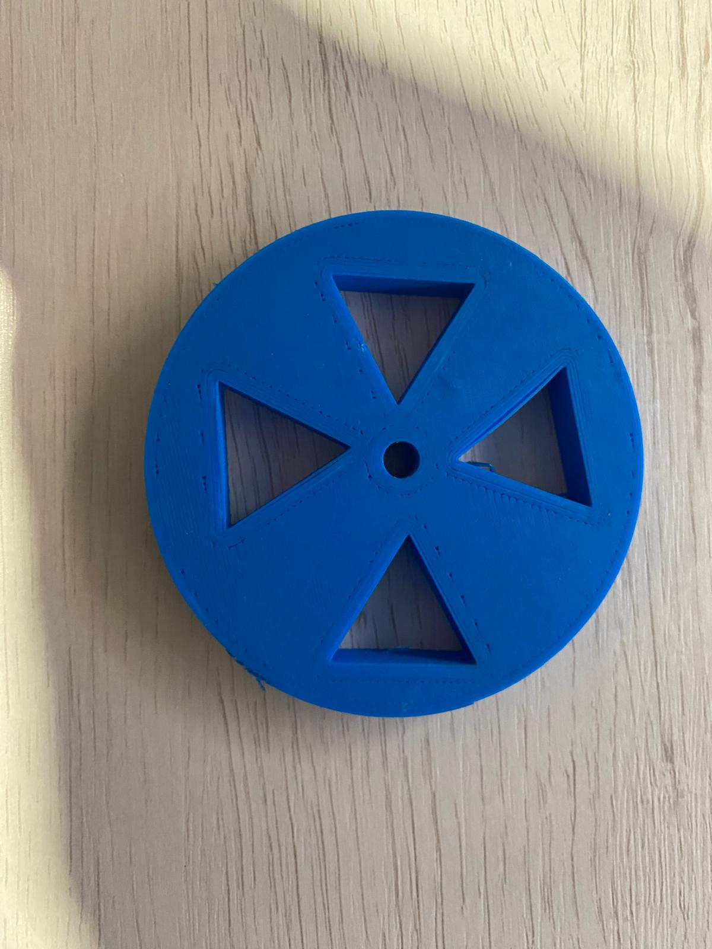
Imagenes/rueda.jpeg
