RoboticsURJC/tfg-vdelatorre/Imagenes/rueda.png

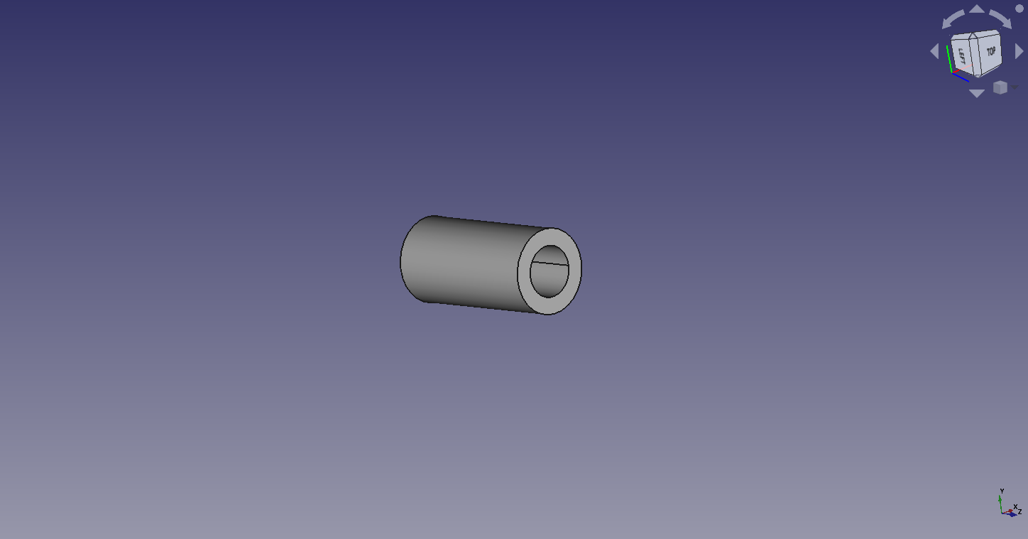
Imagenes/rueda.png
