RoboticsURJC/tfg-vdelatorre/Imagenes/rueda_freecad.png

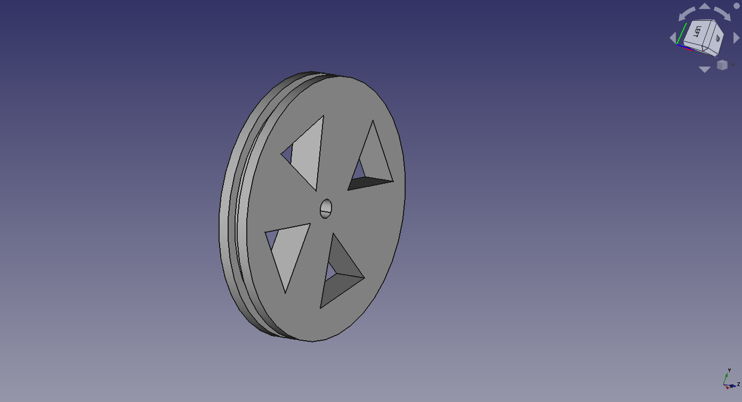
Imagenes/rueda_freecad.png
