RoboticsURJC/tfg-vdelatorre/Imagenes/rueda_junta.jpeg

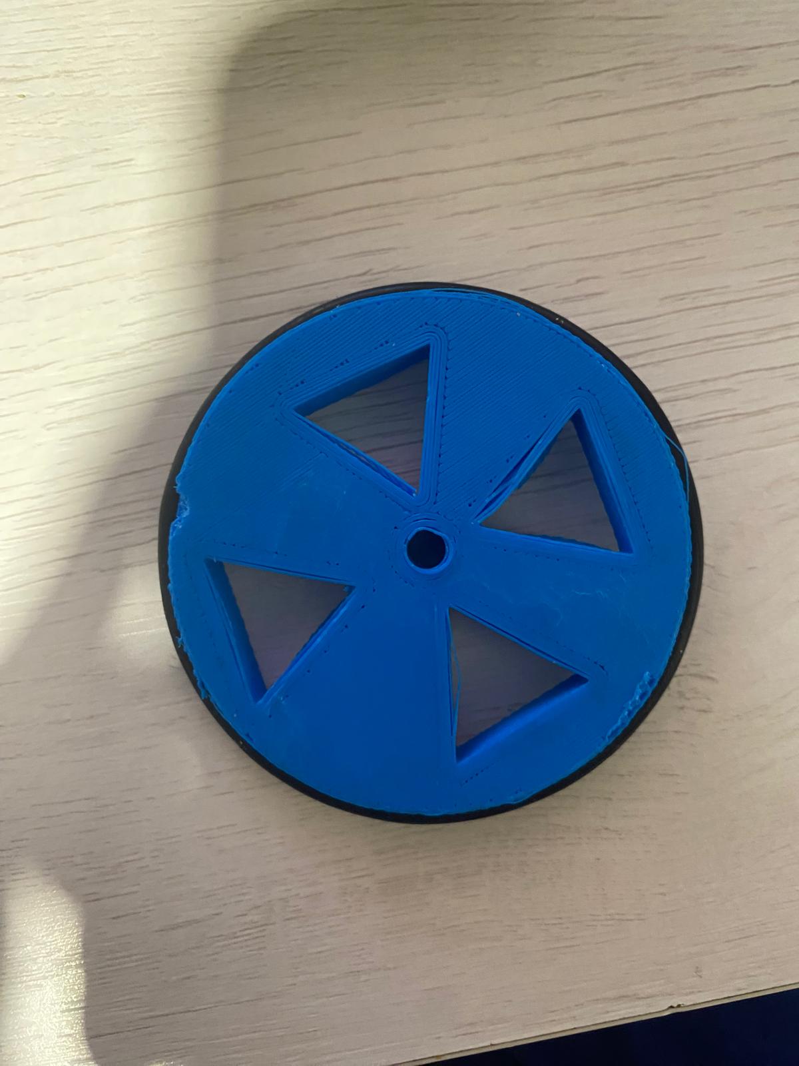
Imagenes/rueda_junta.jpeg
