RoboticsURJC/tfg-vdelatorre/Imagenes/trilateracion.jpg

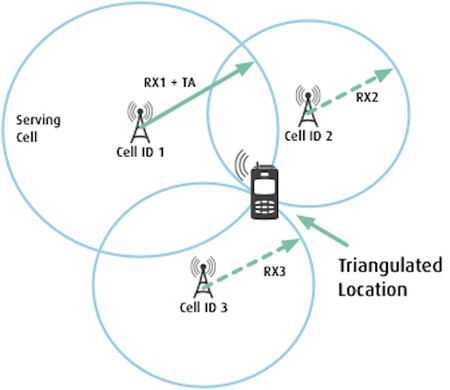
Imagenes/trilateracion.jpg
