RoboticsURJC/tfg-vdelatorre/Imagenes/tubo_mejorado.jpeg

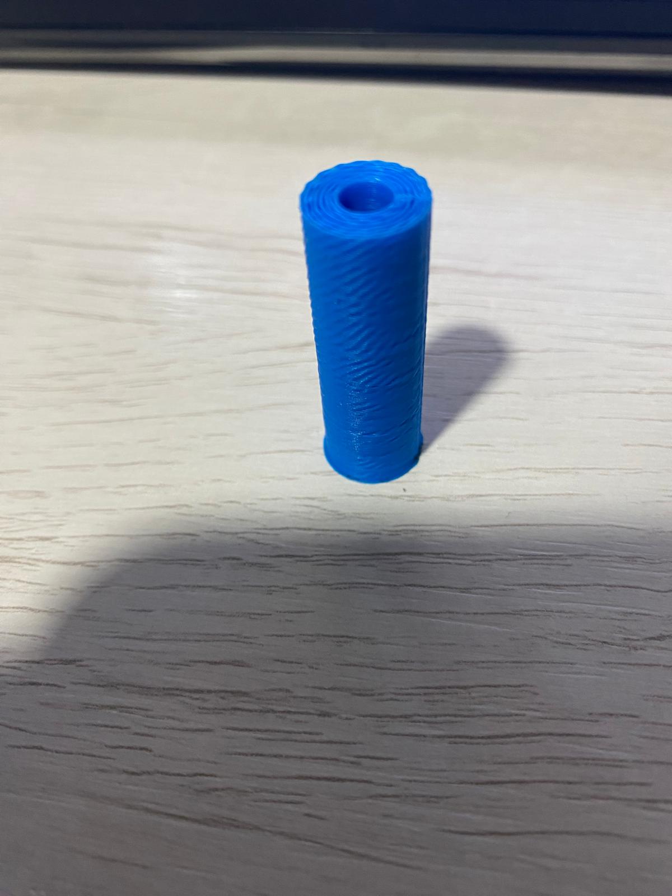
Imagenes/tubo_mejorado.jpeg
