RoboticsURJC/tfg-vdelatorre/Imagenes/vnc2.png

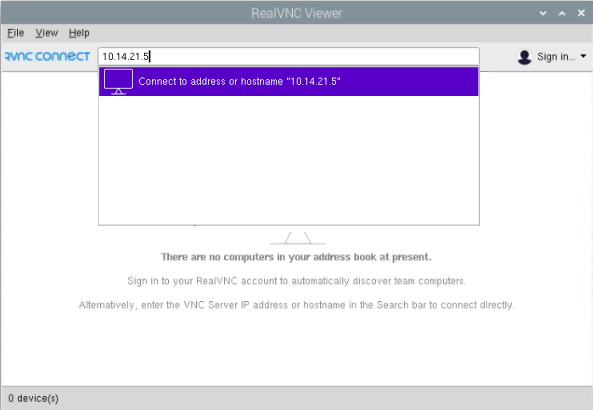
Imagenes/vnc2.png
