RoboticsURJC/tfg-vdelatorre/Imagenes/vnc3.png

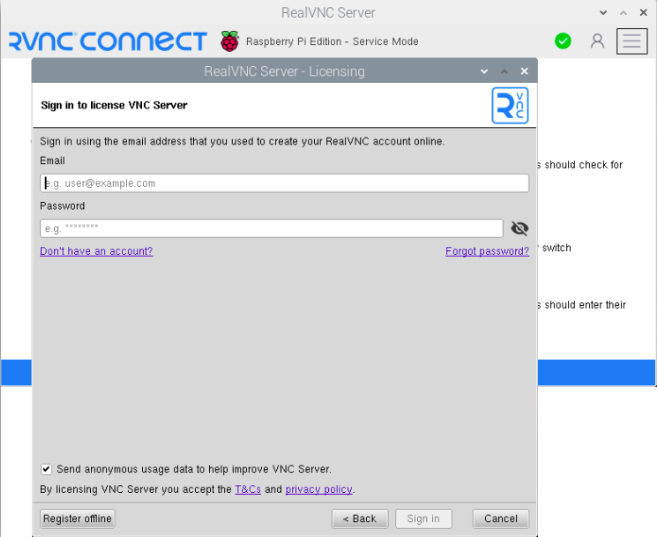
Imagenes/vnc3.png
