RoboticsURJC/tfg-vdelatorre/Imagenes/vnc4.png

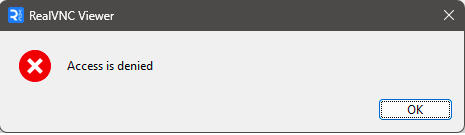
Imagenes/vnc4.png
