RoboticsURJC/tfg-vdelatorre/Imagenes/vnc5.png

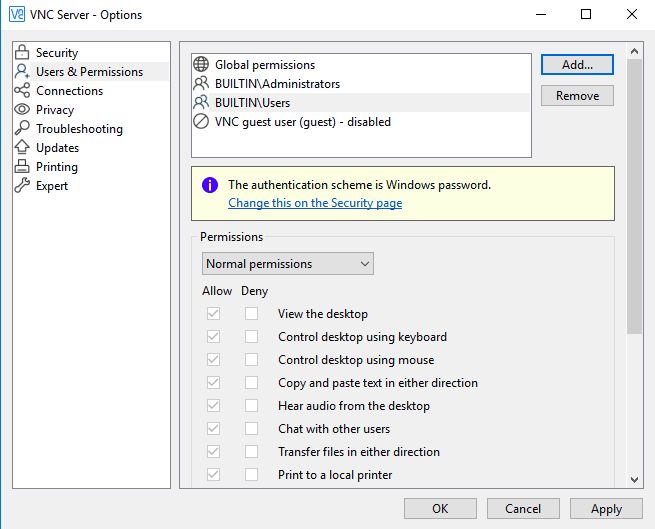
Imagenes/vnc5.png
