RoboticsURJC/tfg-vdelatorre/Imagenes/vnc6.png

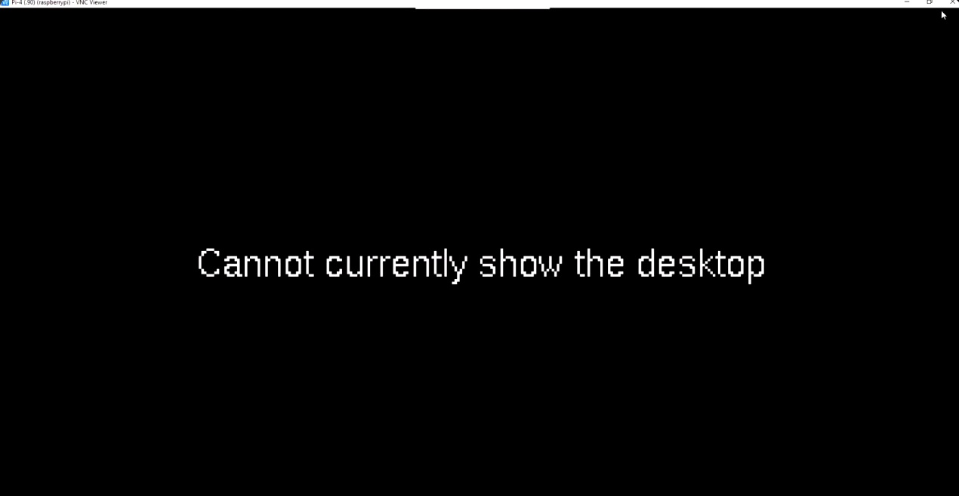
Imagenes/vnc6.png
