RoboticsURJC/tfg-vdelatorre/Imagenes/vnc7.jpeg

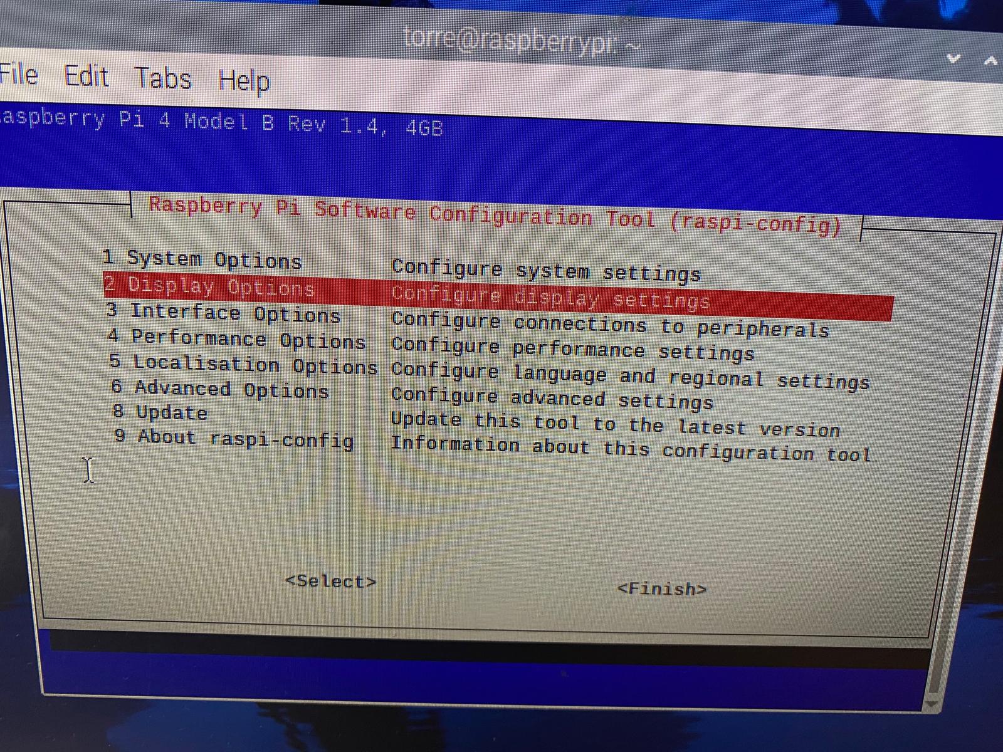
Imagenes/vnc7.jpeg
