RoboticsURJC/tfg-vdelatorre/Imagenes/vnc8.jpeg

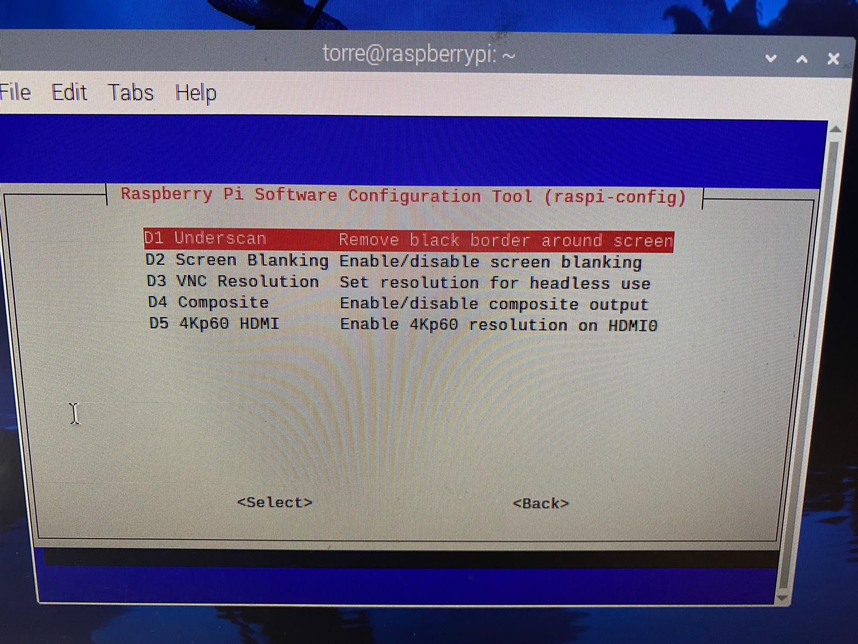
Imagenes/vnc8.jpeg
