RoboticsURJC/tfg-vdelatorre/Imagenes/vnc.png

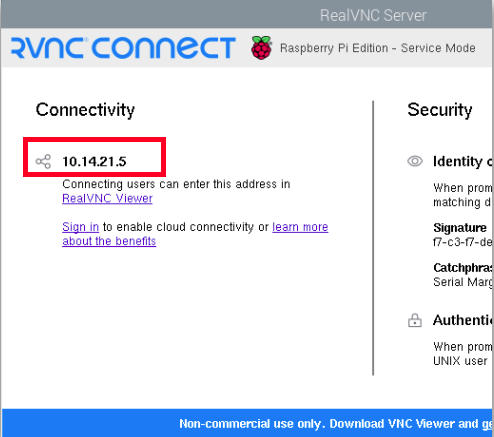
Imagenes/vnc.png
