RoboticsURJC/tfg-vdelatorre/Imagenes/vpnfinal.png

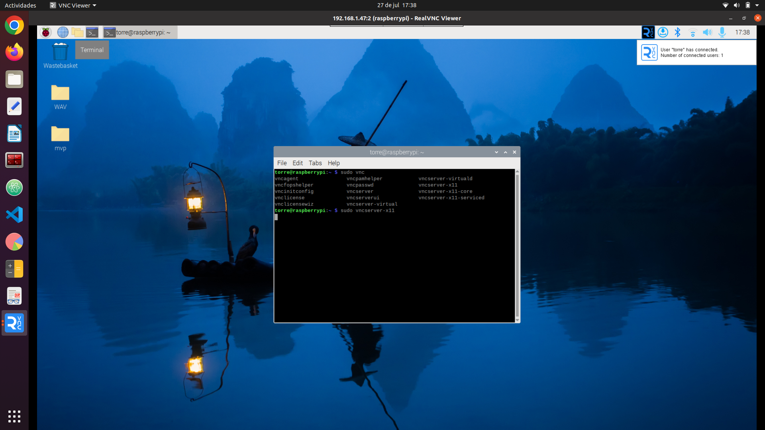
Imagenes/vpnfinal.png
