RoboticsURJC/tfg-vdelatorre/memoria_tfg/figs/astar.jpeg

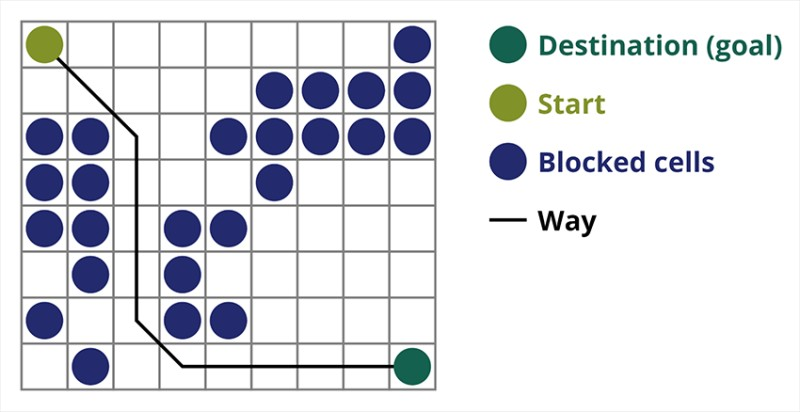
memoria_tfg/figs/astar.jpeg
