RoboticsURJC/tfg-vdelatorre/memoria_tfg/figs/boe-bot-parallax.png

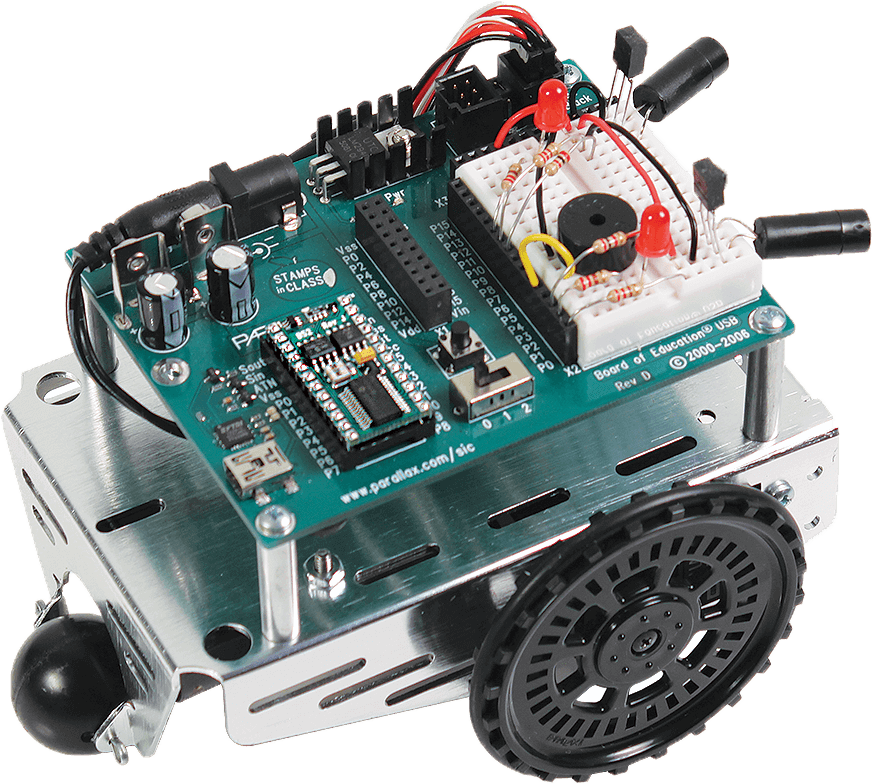
memoria_tfg/figs/boe-bot-parallax.png
