RoboticsURJC/tfg-vdelatorre/memoria_tfg/figs/circuit_image.png

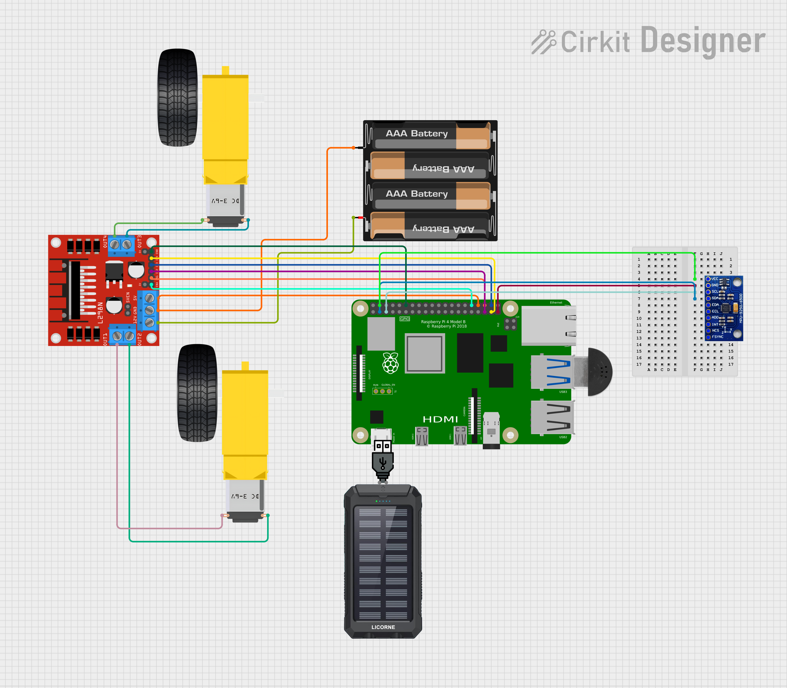
memoria_tfg/figs/circuit_image.png
