RoboticsURJC/tfg-vdelatorre/memoria_tfg/figs/circuito.png

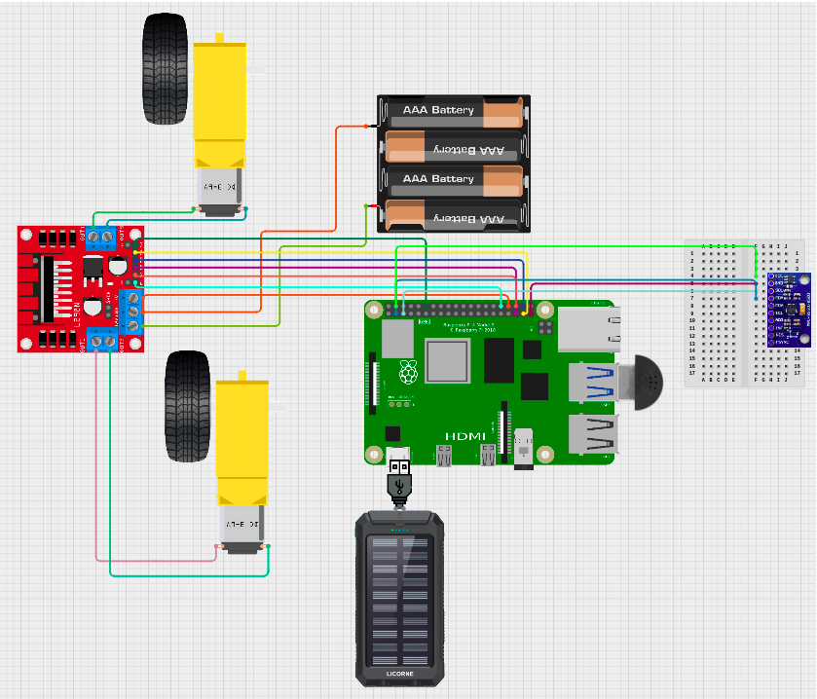
memoria_tfg/figs/circuito.png
