RoboticsURJC/tfg-vdelatorre/memoria_tfg/figs/escenario.jpeg

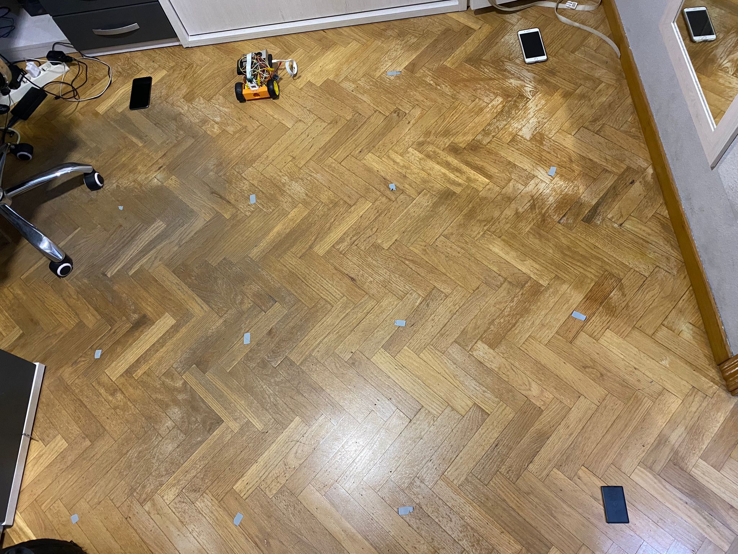
memoria_tfg/figs/escenario.jpeg
