RoboticsURJC/tfg-vdelatorre/memoria_tfg/figs/jup1.png

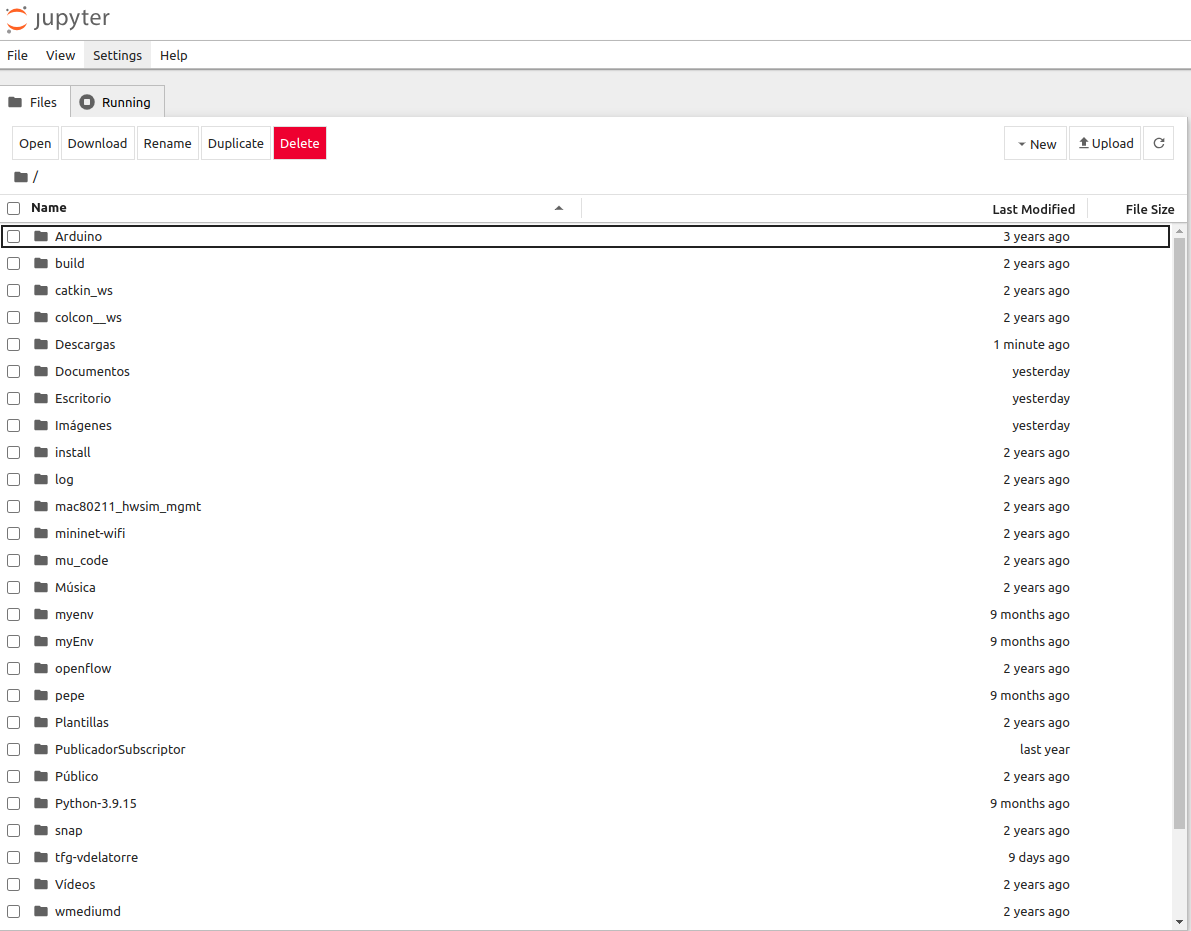
memoria_tfg/figs/jup1.png
