RoboticsURJC/tfg-vdelatorre/memoria_tfg/figs/jup2.png

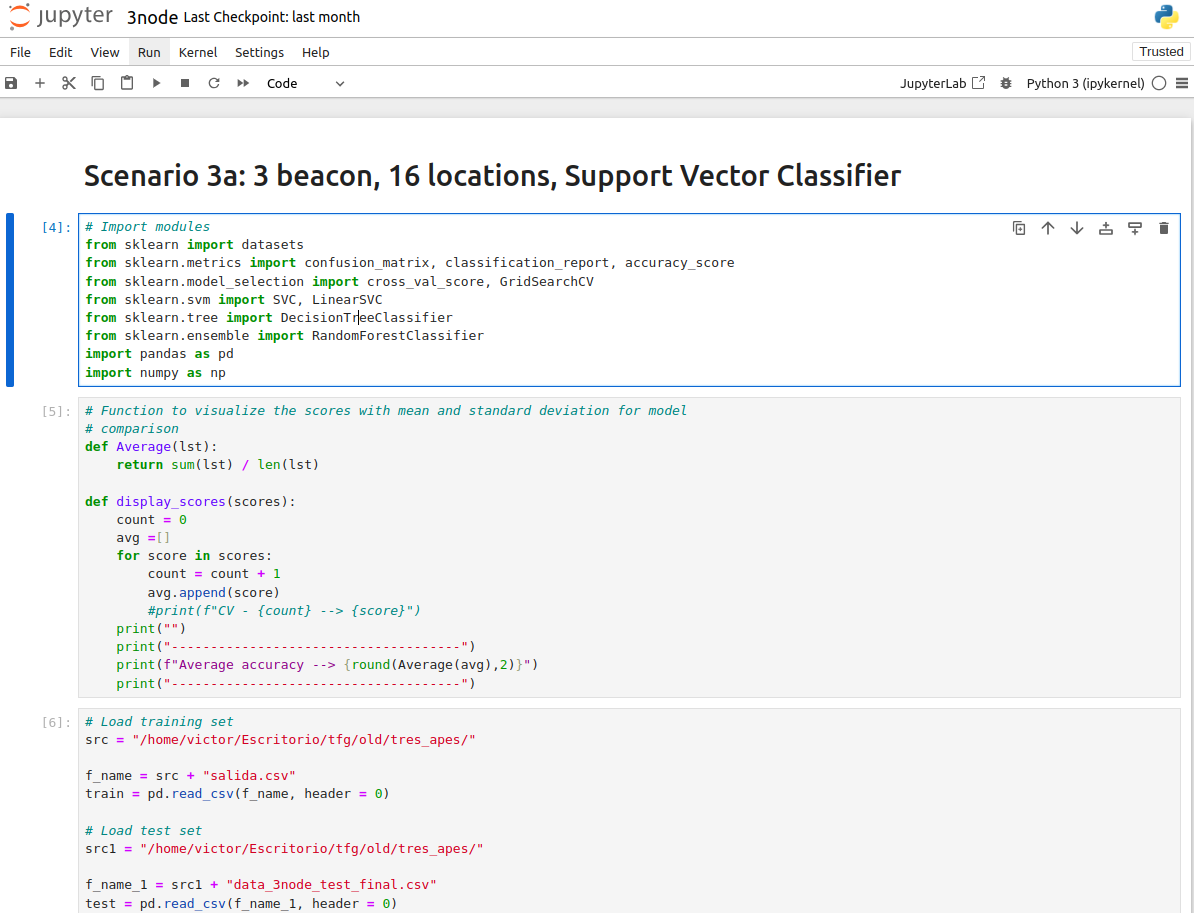
memoria_tfg/figs/jup2.png
