RoboticsURJC/tfg-vdelatorre/memoria_tfg/figs/kuka.jpeg

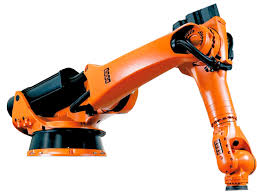
memoria_tfg/figs/kuka.jpeg
