RoboticsURJC/tfg-vdelatorre/memoria_tfg/figs/rasps.jpeg

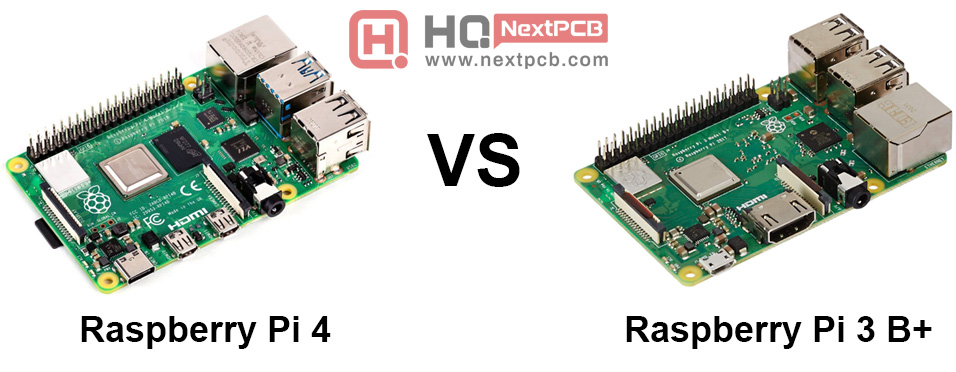
memoria_tfg/figs/rasps.jpeg
