RoboticsURJC/tfg-vdelatorre/presentacion_tfg/figs/turtle.jpg

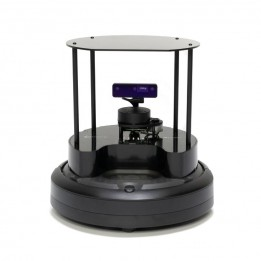
presentacion_tfg/figs/turtle.jpg
