RoboticsURJC/tfg-vdelatorre/final_test/astar.py

import math
import heapq
import matplotlib.pyplot as plt
import random

# Define the Cell class
class Cell:
    def __init__(self):
        self.parent_i = 0  # Parent cell's row index
        self.parent_j = 0  # Parent cell's column index
        self.f = float('inf')  # Total cost of the cell (g + h)
        self.g = float('inf')  # Cost from start to this cell
        self.h = 0  # Heuristic cost from this cell to destination

ROW = 0
COL = 0

# Check if a cell is valid (within the grid)
def is_valid(row, col):
    return (row >= 0) and (row < ROW) and (col >= 0) and (col < COL)

# Check if a cell is unblocked
def is_unblocked(grid, row, col):
    return grid[row][col] == 1

# Check if a cell is the destination
def is_destination(row, col, dest):
    return row == dest[0] and col == dest[1]

# Calculate the heuristic value of a cell (Euclidean distance to destination)
def calculate_h_value(row, col, dest):
    return ((row - dest[0]) ** 2 + (col - dest[1]) ** 2) ** 0.5

# Trace the path from source to destination
def trace_path(cell_details, dest):
    print("The Path is ")
    path = []
    row = dest[0]
    col = dest[1]

    # Trace the path from destination to source using parent cells
    while not (cell_details[row][col].parent_i == row and cell_details[row][col].parent_j == col):
        path.append((row, col))
        temp_row = cell_details[row][col].parent_i
        temp_col = cell_details[row][col].parent_j
        row = temp_row
        col = temp_col

    # Add the source cell to the path
    path.append((row, col))
    # Reverse the path to get the path from source to destination
    path.reverse()

    # Print the path
    for i in path:
        print("->", i, end=" ")
    print()

    return path

# Implement the A* search algorithm
def a_star_search(grid, src, dest):
    # Check if the source and destination are valid
    if not is_valid(src[0], src[1]) or not is_valid(dest[0], dest[1]):
        print("Source or destination is invalid")
        return

    # Check if the source and destination are unblocked
    if not is_unblocked(grid, src[0], src[1]) or not is_unblocked(grid, dest[0], dest[1]):
        print("Source or the destination is blocked")
        return

    # Check if we are already at the destination
    if is_destination(src[0], src[1], dest):
        print("We are already at the destination")
        return

    # Initialize the closed list (visited cells)
    closed_list = [[False for _ in range(COL)] for _ in range(ROW)]
    # Initialize the details of each cell
    cell_details = [[Cell() for _ in range(COL)] for _ in range(ROW)]

    # Initialize the start cell details
    i = src[0]
    j = src[1]
    cell_details[i][j].f = 0
    cell_details[i][j].g = 0
    cell_details[i][j].h = 0
    cell_details[i][j].parent_i = i
    cell_details[i][j].parent_j = j

    # Initialize the open list (cells to be visited) with the start cell
    open_list = []
    heapq.heappush(open_list, (0.0, i, j))

    # Initialize the flag for whether destination is found
    found_dest = False

    # Main loop of A* search algorithm
    while len(open_list) > 0:
        # Pop the cell with the smallest f value from the open list
        p = heapq.heappop(open_list)

        # Mark the cell as visited
        i = p[1]
        j = p[2]
        closed_list[i][j] = True

        # For each direction, check the successors
        directions = [(0, 1), (0, -1), (1, 0), (-1, 0), (1, 1), (1, -1), (-1, 1), (-1, -1)]
        for dir in directions:
            new_i = i + dir[0]
            new_j = j + dir[1]

            # If the successor is valid, unblocked, and not visited
            if is_valid(new_i, new_j) and is_unblocked(grid, new_i, new_j) and not closed_list[new_i][new_j]:
                # If the successor is the destination
                if is_destination(new_i, new_j, dest):
                    # Set the parent of the destination cell
                    cell_details[new_i][new_j].parent_i = i
                    cell_details[new_i][new_j].parent_j = j
                    print("The destination cell is found")
                    # Trace and print the path from source to destination
                    path = trace_path(cell_details, dest)
                    found_dest = True
                    return path
                else:
                    # Calculate the new f, g, and h values
                    g_new = cell_details[i][j].g + 1.0
                    h_new = calculate_h_value(new_i, new_j, dest)
                    f_new = g_new + h_new

                    # If the cell is not in the open list or the new f value is smaller
                    if cell_details[new_i][new_j].f == float('inf') or cell_details[new_i][new_j].f > f_new:
                        # Add the cell to the open list
                        heapq.heappush(open_list, (f_new, new_i, new_j))
                        # Update the cell details
                        cell_details[new_i][new_j].f = f_new
                        cell_details[new_i][new_j].g = g_new
                        cell_details[new_i][new_j].h = h_new
                        cell_details[new_i][new_j].parent_i = i
                        cell_details[new_i][new_j].parent_j = j

    # If the destination is not found after visiting all cells
    if not found_dest:
        print("Failed to find the destination cell")
        return None

def visualize_grid(grid, path,src,dest):
    fig, ax = plt.subplots()

    # Draw the grid
    ax.imshow(grid, cmap=plt.cm.gray)

    # Mark the start and end points
    ax.text(src[1], src[0], 'Start', ha='center', va='center', color='red', fontsize=12)
    ax.text(dest[1], dest[0], 'End', ha='center', va='center', color='blue', fontsize=12)

    # Draw the path
    if path is not None:
        path = [(p[1], p[0]) for p in path]  # Convert (row, col) to (x, y)
        ax.plot([p[0] for p in path], [p[1] for p in path], marker='o', color='green', markersize=3)

    ax.grid(True)
    plt.savefig("astar.png")

def load_image_from_text(file_path):
    grid = []
    with open(file_path, 'r') as file:
        for line in file:
            # Eliminar espacios en blanco al inicio y final de la línea
            line = line.strip()
            # Convertir cada carácter '0' o '1' a un entero 0 o 1
            row = [int(char) for char in line]
            # Agregar la fila a la lista principal (grid)
            grid.append(row)
    return grid

def search_path(prediccion):
    global ROW
    global COL
    # Define the grid (1 for unblocked, 0 for blocked)
    '''
    grid = [
        [1, 1, 1, 1, 1, 1, 1],
        [1, 1, 1, 1, 1, 1, 1],
        [1, 1, 1, 1, 1, 1, 1],
        [1, 1, 1, 1, 1, 1, 1],
        [1, 1, 1, 1, 1, 1, 1]
    ]
    '''
    # Ejemplo de uso
    file_path = '/home/torre/Desktop/mvp/mpu6050/mpu6050/final/matriz_final.txt'  # Ruta a tu archivo de texto
    grid = load_image_from_text(file_path)

    ROW = len(grid)
    COL = len(grid[0])
    print(ROW)
    print(COL)


    # Define the source and destination
    src = [20, 42]

    
    if(prediccion[0] == "habitacion"):
        print("HABITACIONNNN")
        dest = [23,42]
    elif(prediccion[0] == "dormitorio"):
        print("DORMITORIOOOOO")
        dest = [10, 36]
    

    # Run the A* search algorithm
    path = a_star_search(grid, src, dest)
    
    # Visualize the grid and path
    visualize_grid(grid, path, src, dest)
    
    return path


#if __name__ == "__main__":
#    print(main())
